Lorcan-L/cad-deliverables/hw73005-l2000/previews/A01-page-01.png

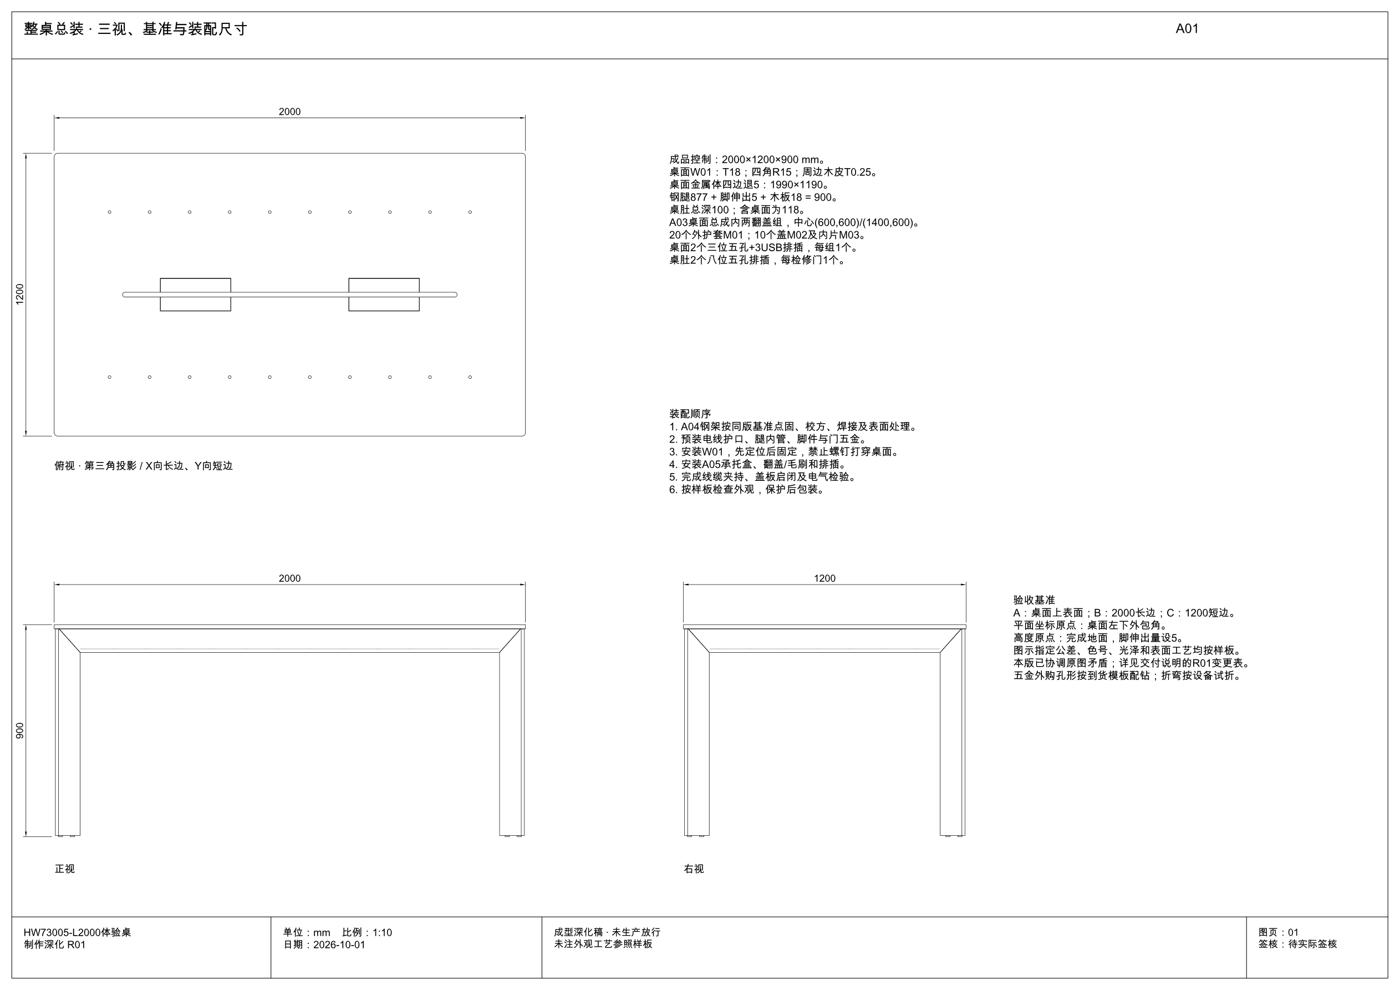
hw73005-l2000/previews/A01-page-01.png
