Lorcan-L/cad-deliverables/hw73005-l2000/previews/A02-page-02.png

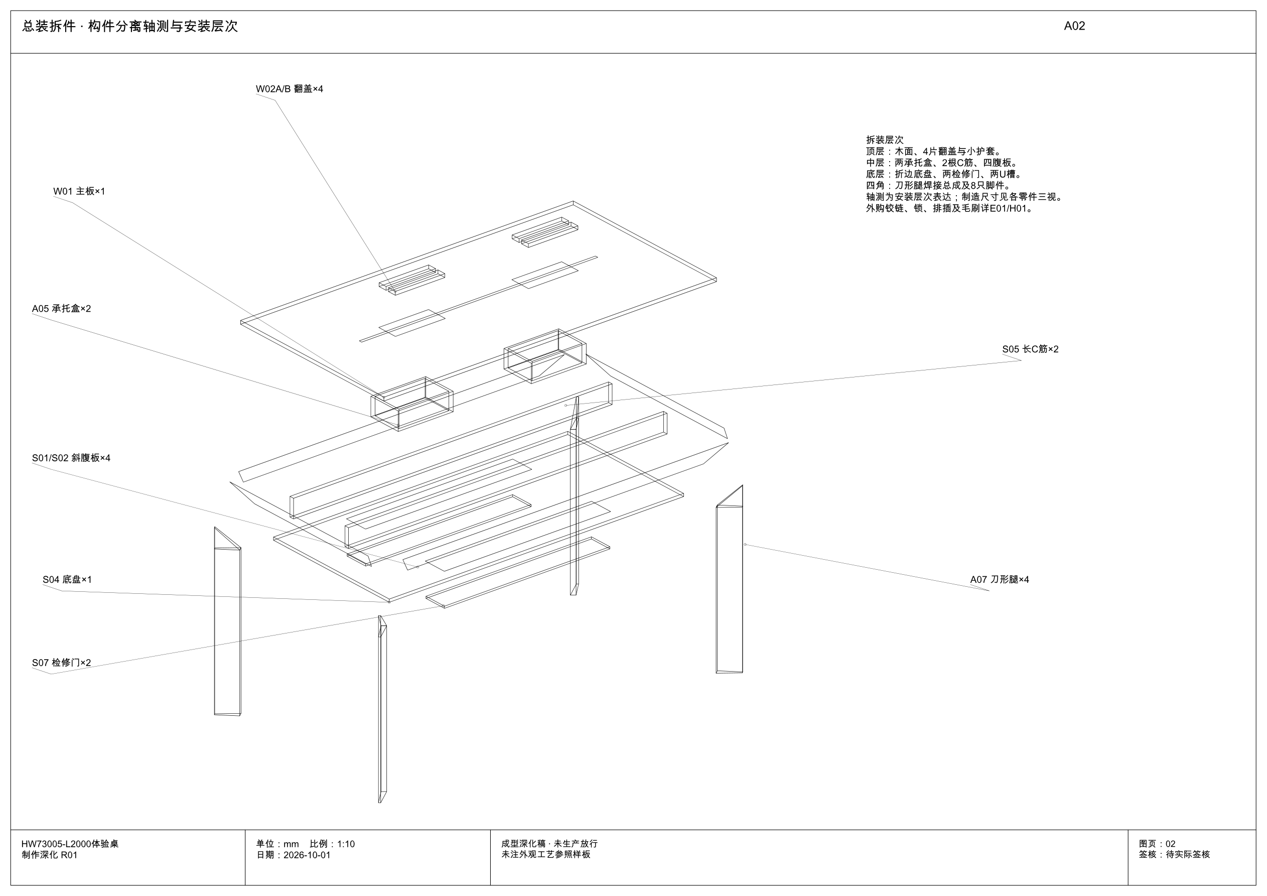
hw73005-l2000/previews/A02-page-02.png
