Lorcan-L/cad-deliverables/hw73005-l2000/previews/M01-page-21.png

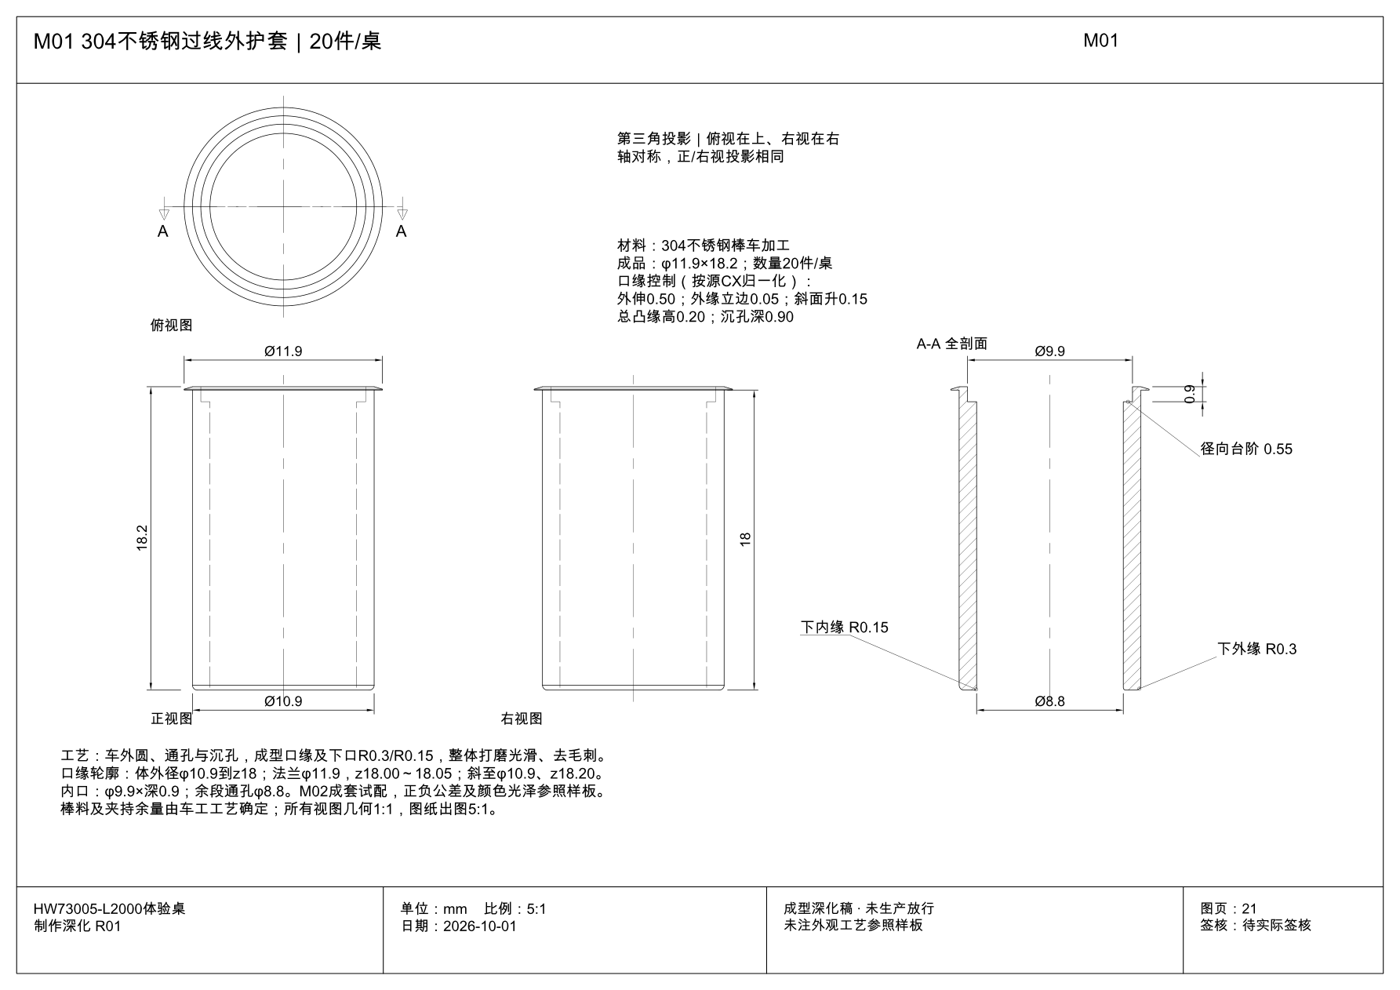
hw73005-l2000/previews/M01-page-21.png
