Lorcan-L/cad-deliverables/hw73005-l2000/previews/R02/A08-page-21.png

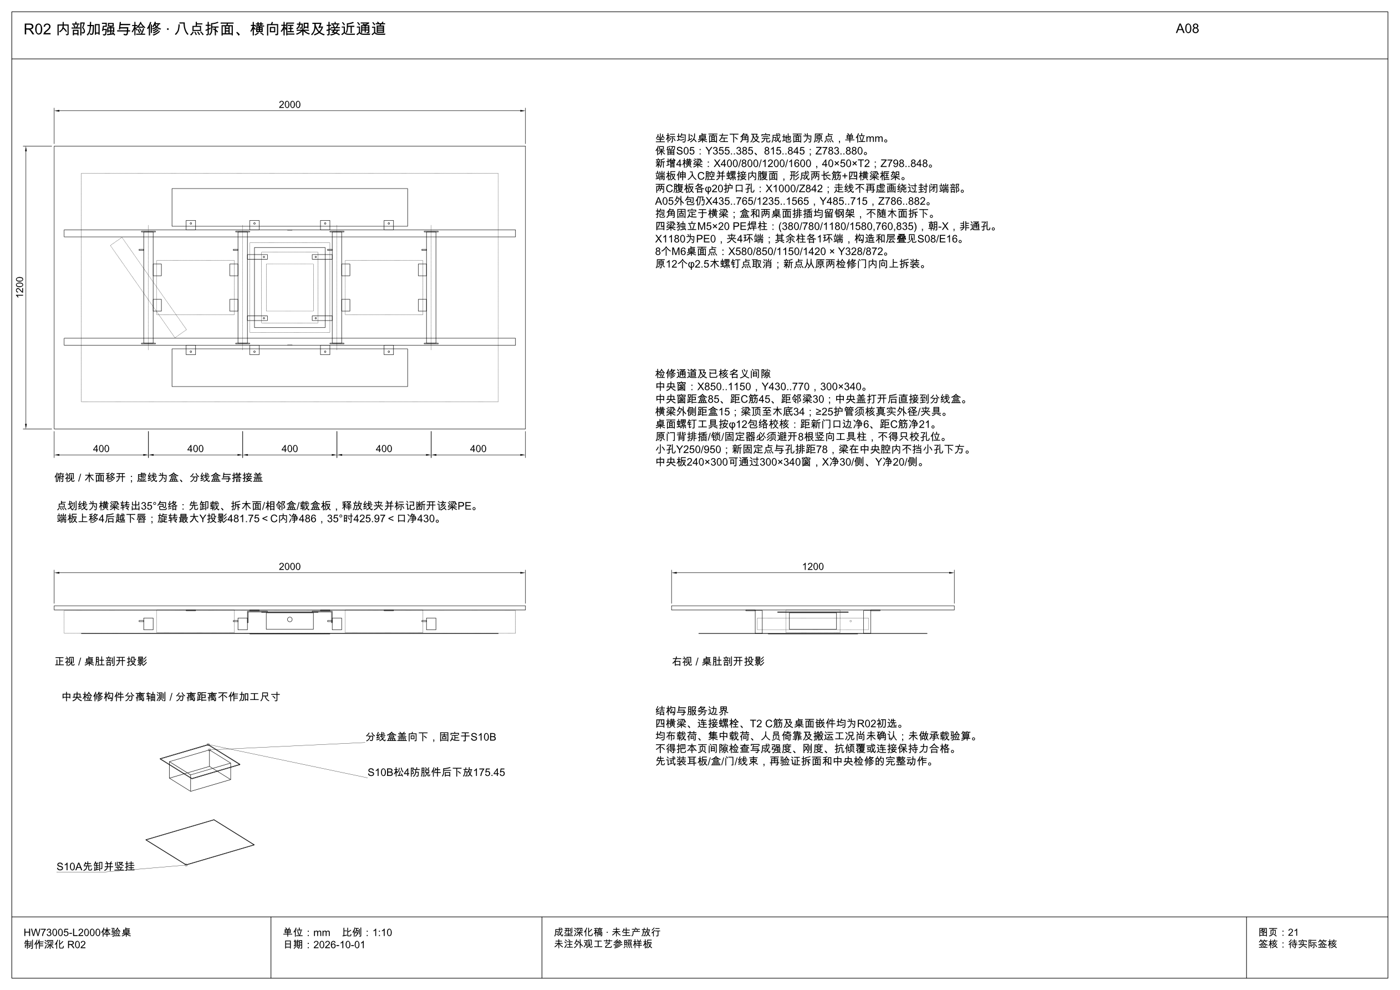
hw73005-l2000/previews/R02/A08-page-21.png
