Lorcan-L/cad-deliverables/hw73005-l2000/previews/R02/E02-page-32.png

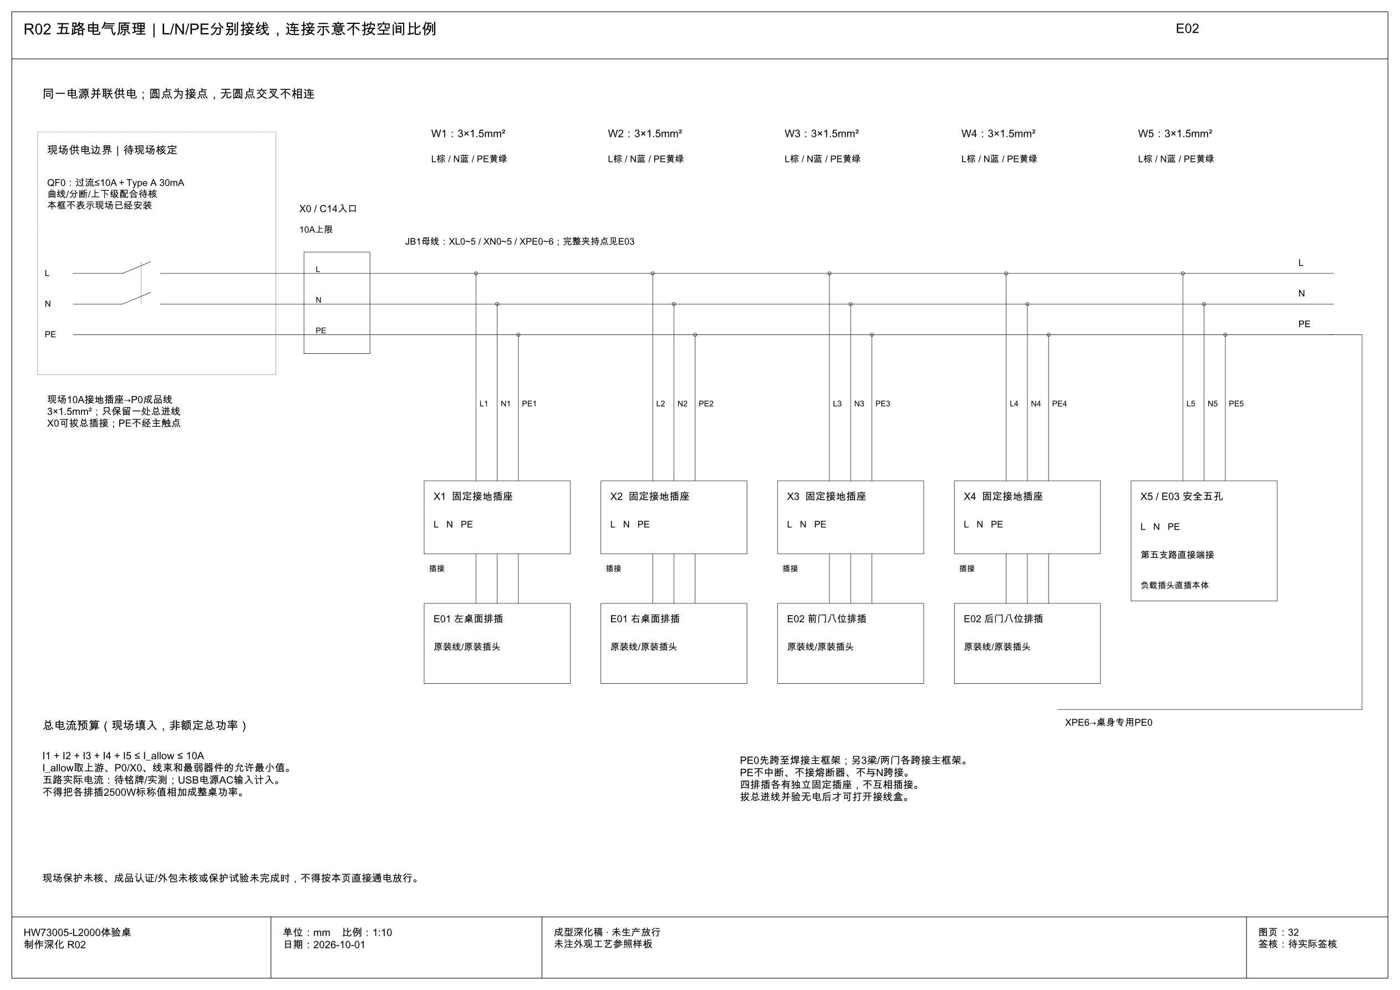
hw73005-l2000/previews/R02/E02-page-32.png
