Lorcan-L/cad-deliverables/hw73005-l2000/previews/R02/S10F-page-29.png

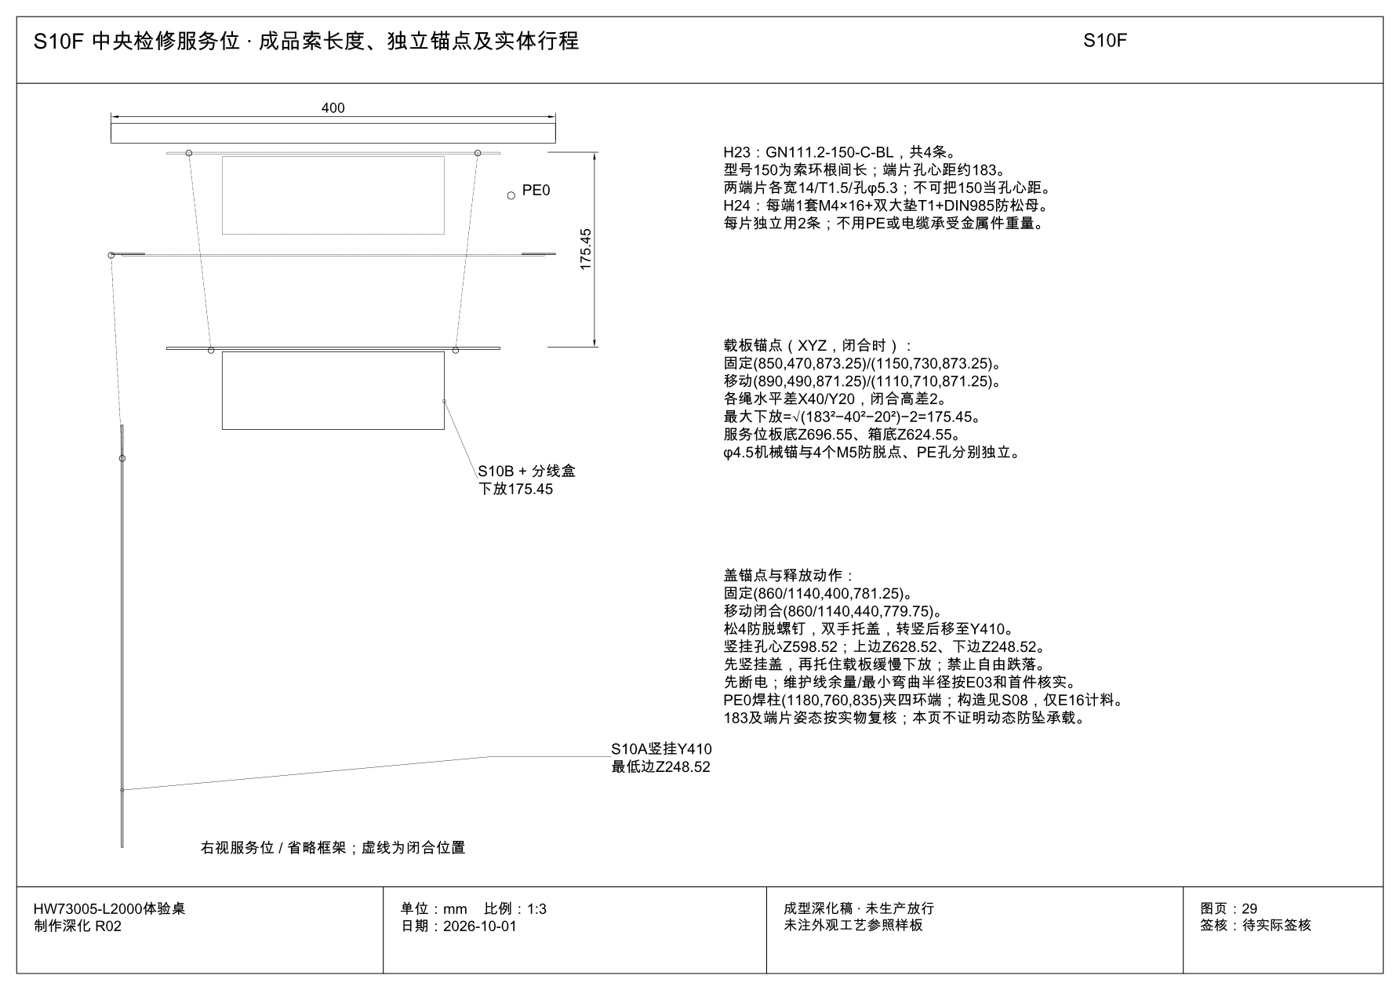
hw73005-l2000/previews/R02/S10F-page-29.png
