Lorcan-L/cad-deliverables/hw73005-l2000/previews/R03/D01-page-15.png

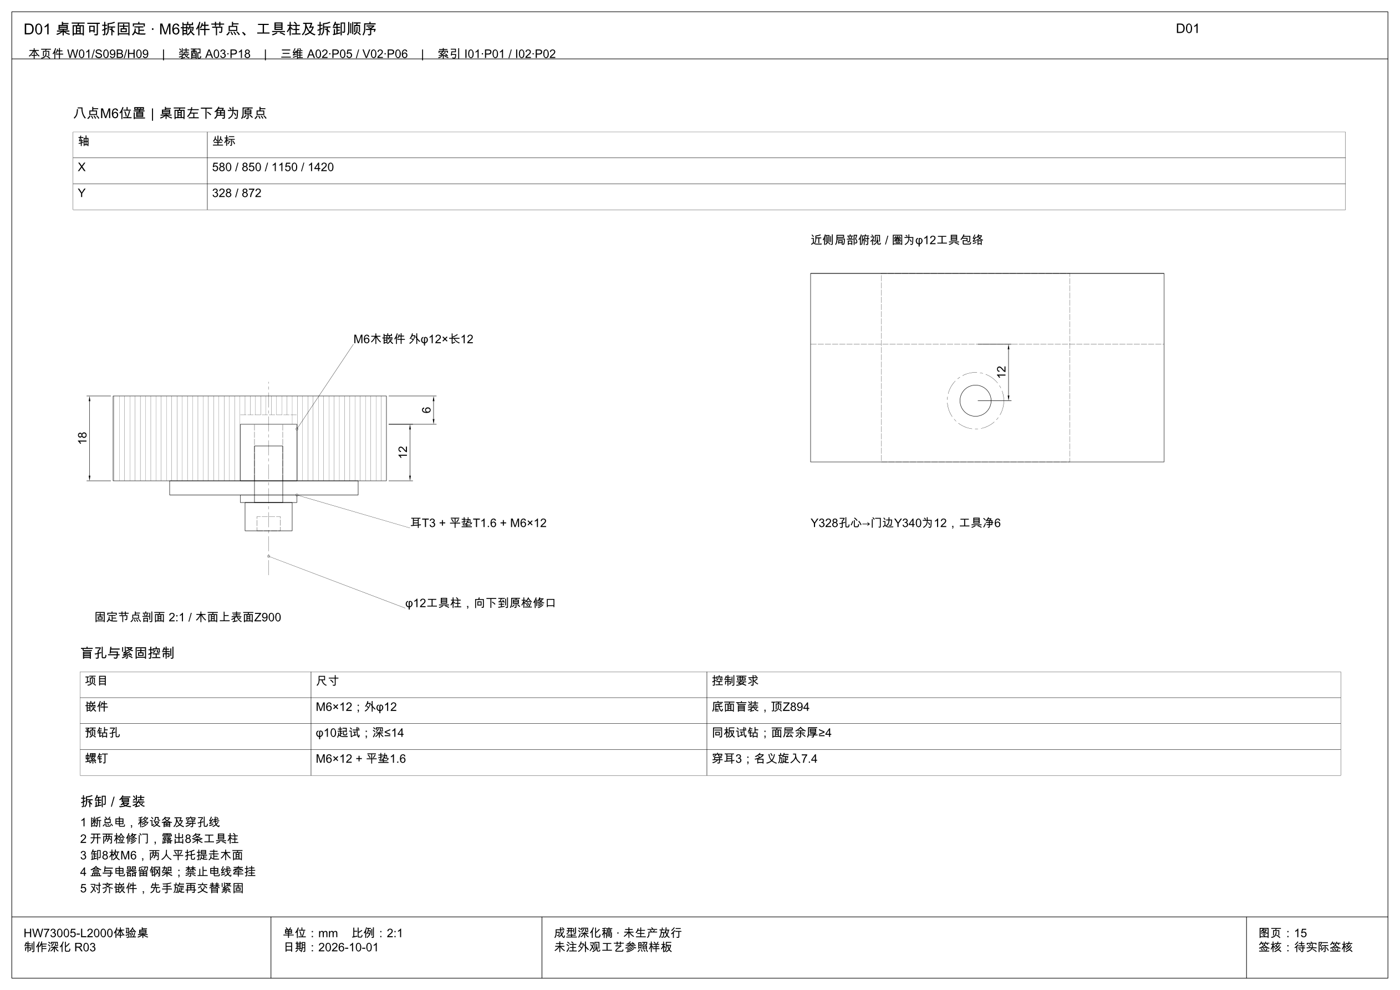
hw73005-l2000/previews/R03/D01-page-15.png
