Lorcan-L/cad-deliverables/hw73005-l2000/previews/R03/V05-page-10.png

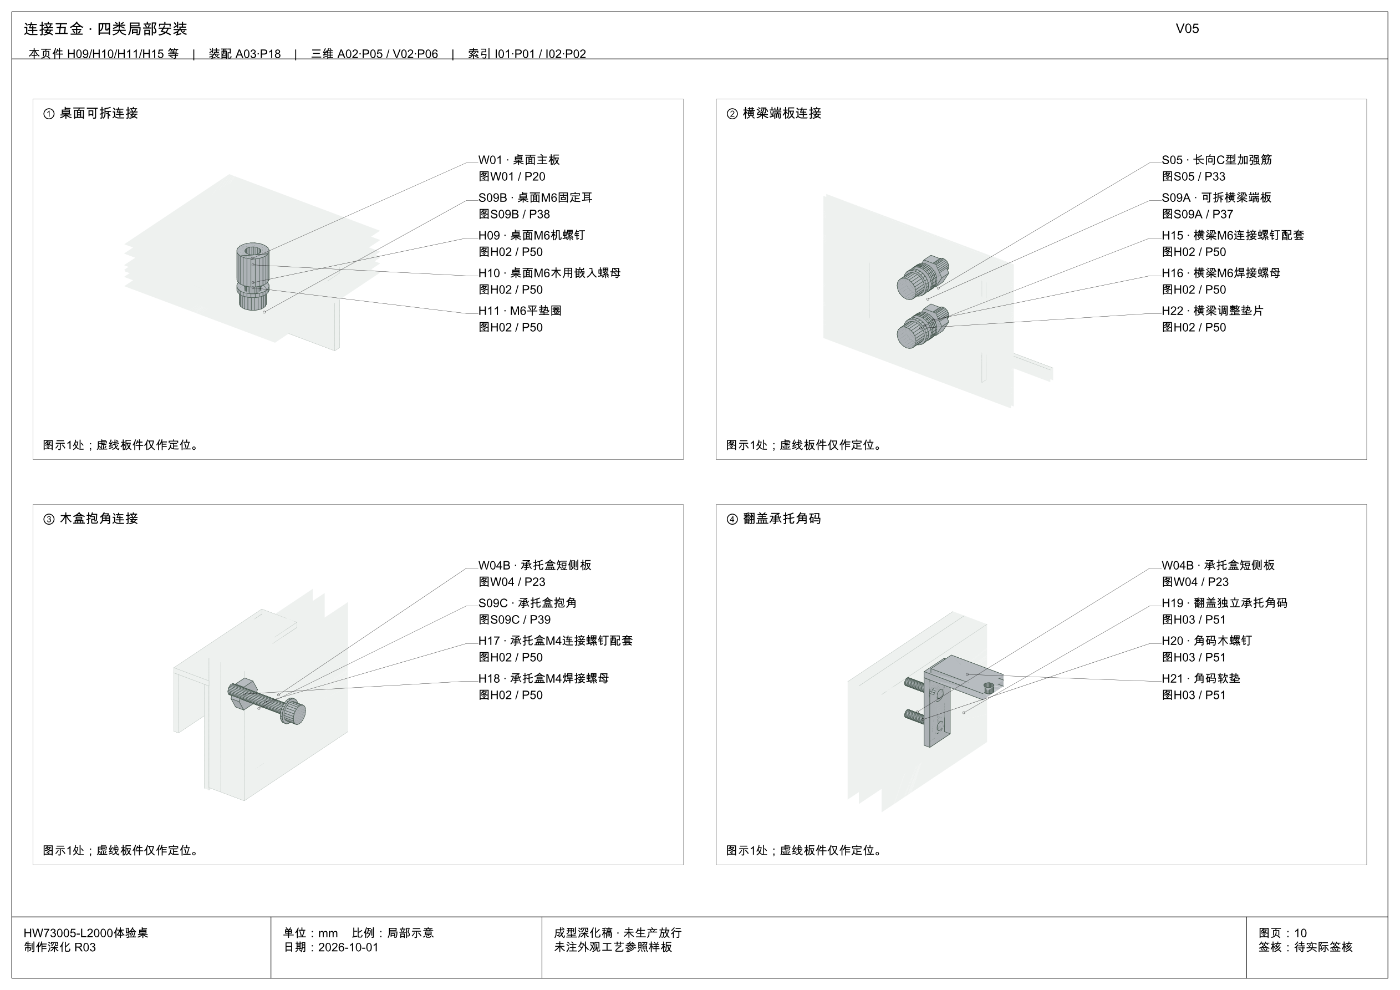
hw73005-l2000/previews/R03/V05-page-10.png
