Lorcan-L/cad-deliverables/hw73005-l2000/previews/R03/V10-page-07.png

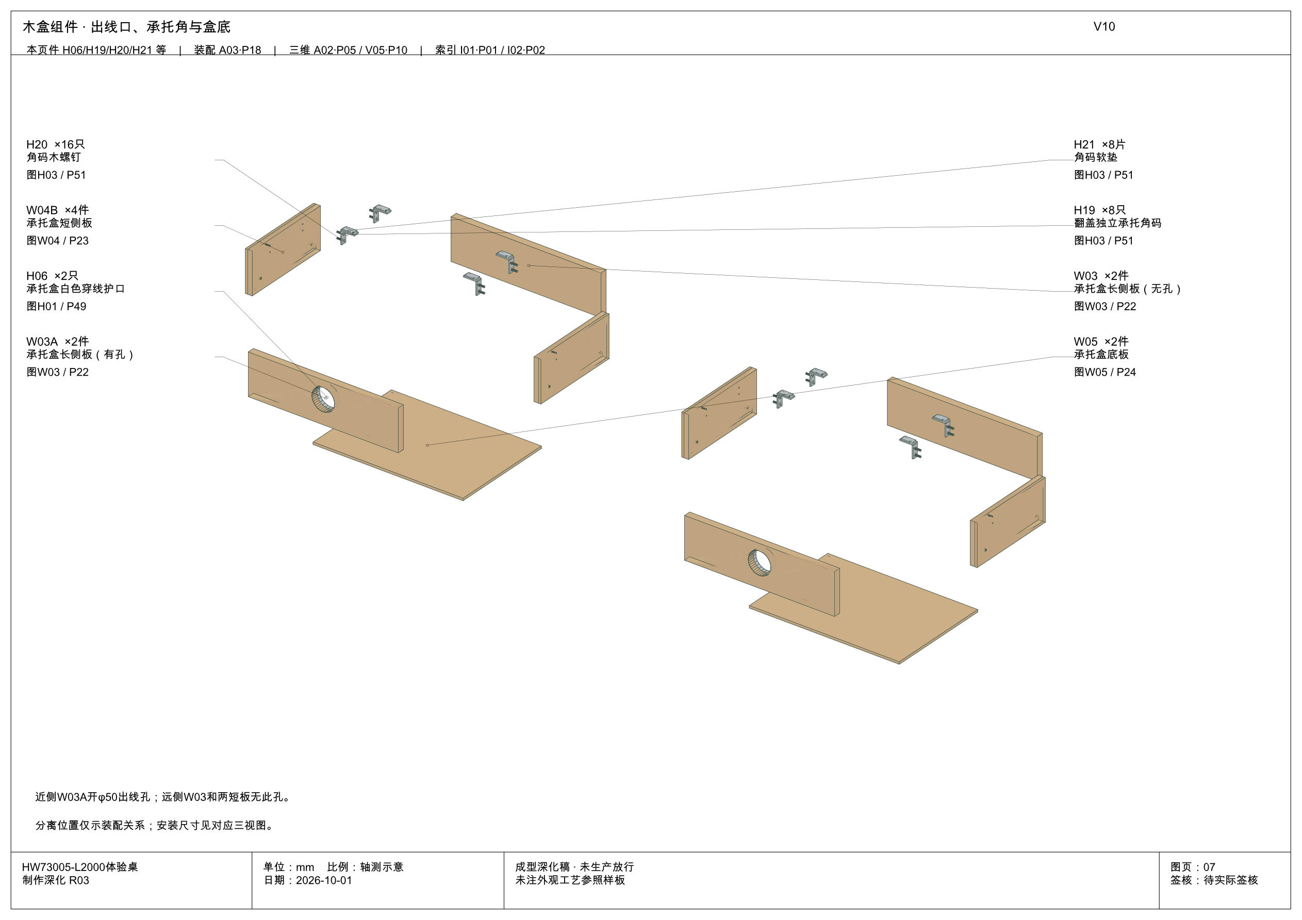
hw73005-l2000/previews/R03/V10-page-07.png
