Lorcan-L/cad-deliverables/hw73005-l2000/previews/R04/page-10.png

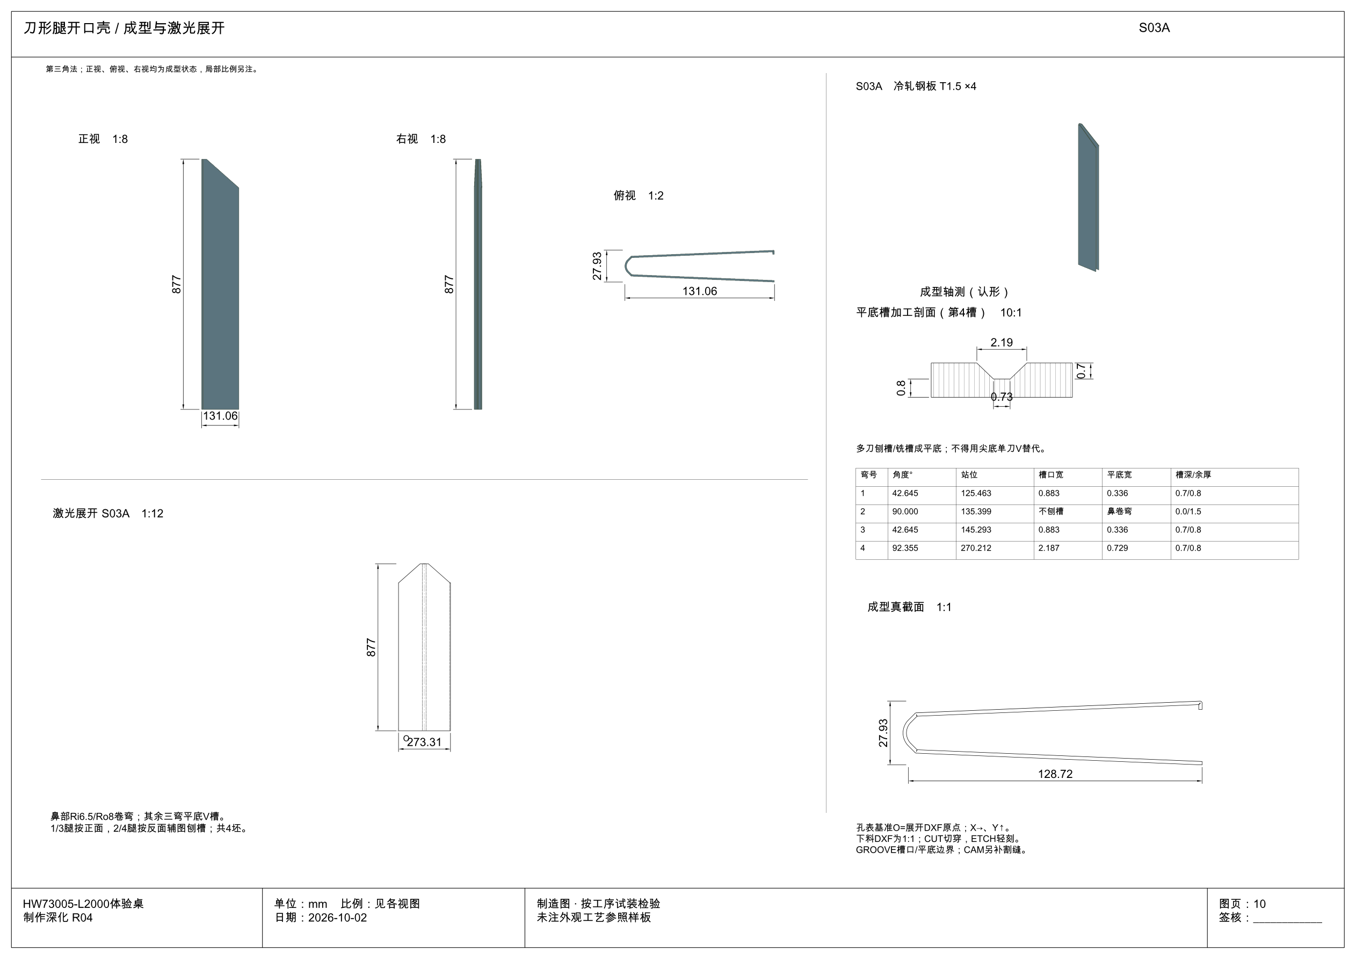
hw73005-l2000/previews/R04/page-10.png
