Lorcan-L/cad-deliverables/hw73005-l2000/previews/W01-page-06.png

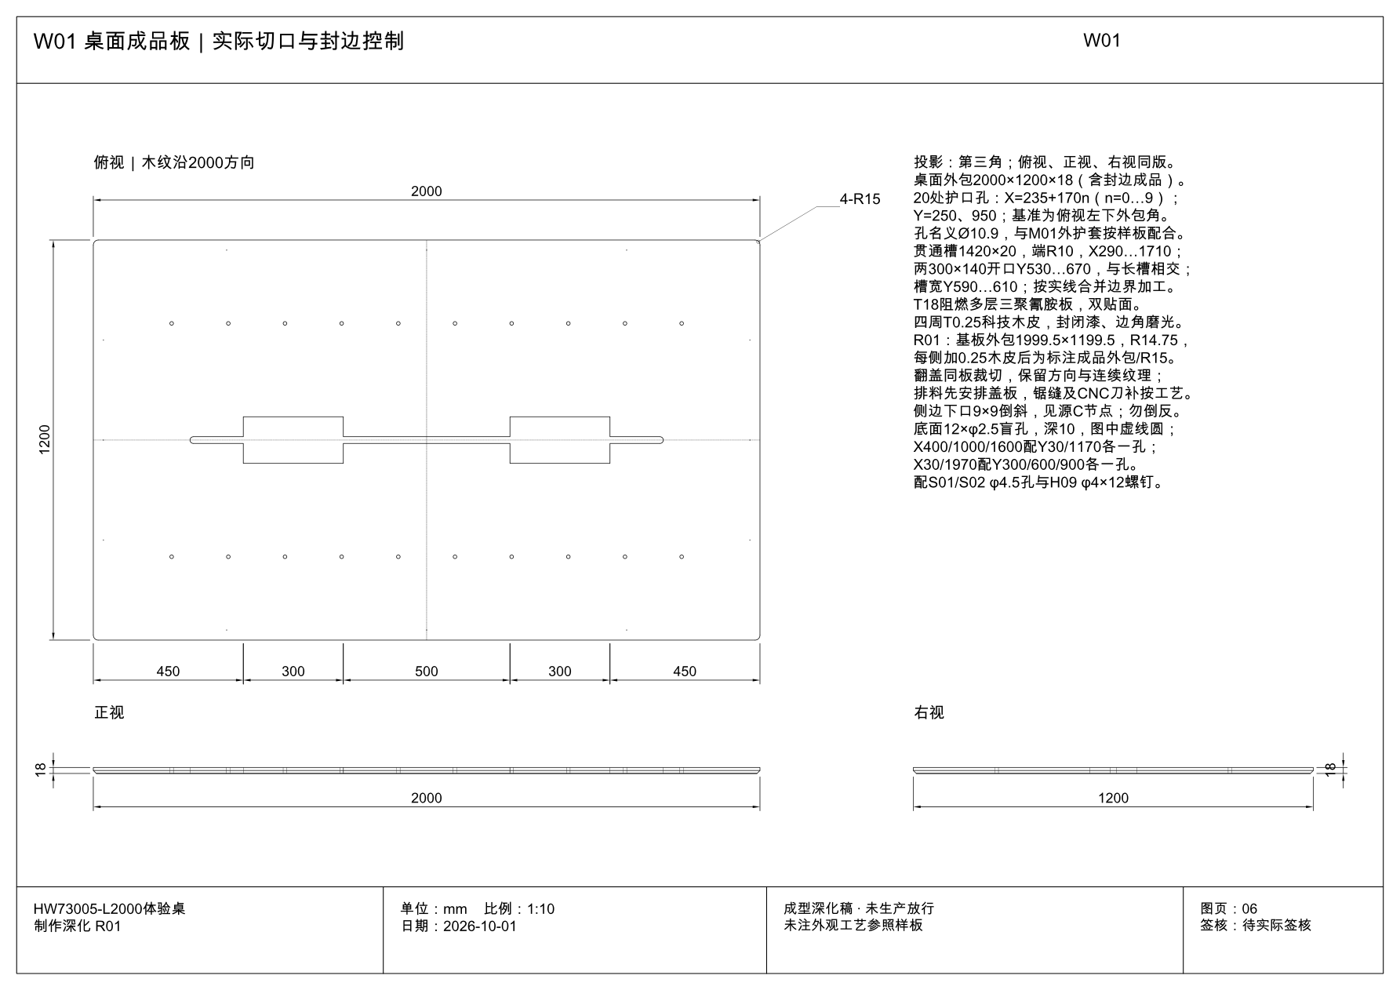
hw73005-l2000/previews/W01-page-06.png
