Lorcan-L/cad-deliverables/hw73005-l2000/files/R03/HW73005-L2000_R03_BOM.xlsx

Sheet: 零件清单
体验桌零件与采购清单
HW73005-L2000 L2000体验桌 R03 尺寸单位 mm
批量（套） | 1 |  | 版次日期 | 2026-10-01
黄色单元格为本批套数。本批数量 = 单套数量 × 套数；空白数量表示待核实。总成与子件不叠加汇总。
编号 | 零件名称 | 所属总成 | 制造 / 采购类别 | 材料 | 厚度 mm | 单套数量 | 单位 | 本批数量 | 成品尺寸 mm | 开料尺寸 mm | 工艺 / 表面处理 | 图号 | PDF 页 | 状态 | 计数口径 | 依据 | 备注
A01 | 体验桌总装 | 整桌 | 装配 | 详见子件 |  | 1 | 套 | 1 | 2000×1200×900 |  | 按图装配→试装检验 | A01 | 4 | 图纸数字核对；实物首件未执行 | 装配数量；材料按子件领用 | 顾客DWG；R02成型与检修协调 | 总成数量不重复计入领料
A04 | 焊接钢结构总成 | A01 | 装配 | 详见子件 |  | 1 | 套 | 1 | 1990×1190×882（含脚） |  | 按图装配→试装检验 | A04 | 17 | 图纸数字核对；实物首件未执行 | 装配数量；材料按子件领用 | 顾客DWG；R02成型与检修协调 | 总成数量不重复计入领料
A03 | 桌面翻盖总成 | A01 | 装配 | 阻燃多层三聚氰胺板+科技木皮 | 18 | 1 | 组 | 1 | 2000×1200×18 | 不另计材料 | 同板裁切、开槽、钻孔、封边、磨边 | A03 | 18 | 成型三视已绘；五金安装按实物配孔 | 装配数量；材料按子件领用 | 原图总装顶视及D节点；R02成品五金与可拆固定修订 | 成品含封边；R02护口孔Ø14+0.5/0；底面八点M6嵌母，按D01定位。取消原12处木螺钉孔。
A05 | 翻盖承托盒总成 | A04 | 装配 | 阻燃多层板 |  | 2 | 组 | 2 | 330×230×96；内净300×200 | 不另计材料 | 侧板围合、底板托底；M4可拆固定至钢架抱角 | A05 | 19 | 成型三视已绘；五金安装按实物配孔 | 装配数量；材料按子件领用 | 原图总装顶视及D节点；R02成品五金与可拆固定修订 | 盒留钢架；W03A长侧φ50孔朝Y485，孔心Z842。
W01 | 桌面主板 | A03 | 木作 | 阻燃多层三聚氰胺板+科技木皮 | 18 | 1 | 件 | 1 | 2000×1200×18 | 基板1999.5×1199.5×18，四周封T0.25木皮 | 同板裁切、开槽、钻孔、封边、磨边 | W01 | 20 | 成型三视已绘；五金安装按实物配孔 | 制造零件数量 | 原图总装顶视及D节点；R02成品五金与可拆固定修订 | 成品含封边；R02护口孔Ø14+0.5/0；底面八点M6嵌母，按D01定位。取消原12处木螺钉孔。
W02A | 桌面有槽翻盖板 | A03 | 木作 | 同桌面T18阻燃多层三聚氰胺板 | 18 | 2 | 件 | 2 | 298×58×18，底侧28×7让位 | 同W01原板顺纹裁切；保留锯缝工艺量 | 同板取料、开让位、磨边、五金配孔 | W02 | 21 | 成型三视已绘；五金安装按实物配孔 | 制造零件数量 | 原图总装顶视及D节点；R02成品五金与可拆固定修订 | 源D 0x8469…0x846e；R01长度298；安装在开口Y低值侧，槽口朝中央毛刷。
W02B | 桌面实截面翻盖板 | A03 | 木作 | 同桌面T18阻燃多层三聚氰胺板 | 18 | 2 | 件 | 2 | 298×58×18，实截面 | 同W01原板顺纹裁切；保留锯缝工艺量 | 同板取料、磨边、五金配孔 | W02 | 21 | 成型三视已绘；五金安装按实物配孔 | 制造零件数量 | 原图总装顶视及D节点；R02成品五金与可拆固定修订 | 源D 0x8465…0x8468；R01长度298；安装在开口Y高值侧，不复制A盖让位槽。
W03 | 承托盒长侧板（无孔） | A05 | 木作 | 阻燃多层板 | 15 | 2 | 件 | 2 | 330×91×15 | 按成品净形 | 裁切、磨边、饰面、试装配孔 | W03 | 22 | 成型三视已绘；五金安装按实物配孔 | 制造零件数量 | 原图总装顶视及D节点；R02成品五金与可拆固定修订 | 远侧Y700..715，每盒1片。
W03A | 承托盒长侧板（有孔） | A05 | 木作 | 阻燃多层板 | 15 | 2 | 件 | 2 | 330×91×15，φ50孔中心165/51 | 按成品净形 | 裁切、开φ50孔、护口试装、磨边 | W03 | 22 | 成型三视已绘；五金安装按实物配孔 | 制造零件数量 | 原图总装顶视及D节点；R02成品五金与可拆固定修订 | 近侧Y485..500；孔心全局(600/1400,492.5,842)，孔朝-Y。
W04B | 承托盒短侧板 | A05 | 木作 | 阻燃多层板 | 15 | 4 | 件 | 4 | 200×91×15 | 按成品净形 | 裁切、2×φ4.5通孔、4×φ2深10盲孔、磨边 | W04 | 23 | 成型三视已绘；五金安装按实物配孔 | 制造零件数量 | 原图总装顶视及D节点；R02成品五金与可拆固定修订 | 固定孔u25/175 v24；承托盲孔u52/148 v64.77/77.77。无过线孔。
W05 | 承托盒底板 | A05 | 木作 | R01选用阻燃多层板 | 5 | 2 | 件 | 2 | 330×230×5 | 按成品净形 | 裁切、磨边、围板托底装配 | W05 | 24 | 成型三视已绘；五金安装按实物配孔 | 制造零件数量 | 原图总装顶视及D节点；R02成品五金与可拆固定修订 | T5为源D节点实线归一结果；材质选用在R01声明。
S01 | 长边斜腹板 | A04 | 钣金 | 冷轧钢板 | 1.5 | 2 | 件 | 2 | 上口1958.5 / 下口1779.06 × 高100；截面横包110.3 | 按成型图、实际板材与折弯机试折反算 | 激光切割→折弯/成型→端口放样→点固校方→焊接打磨→按样板表面处理 | S01 | 26 | 成型控制；展开补偿按设备首件 | 制造零件数量 | 顾客DWG有效图形 + R01分片 | 颜色、光泽、焊缝处理按样板；去毛刺、不得割手
S02 | 短边斜腹板 | A04 | 钣金 | 冷轧钢板 | 1.5 | 2 | 件 | 2 | 上口1158.5 / 下口979.056 × 高100；截面横包110.3 | 按成型图、实际板材与折弯机试折反算 | 激光切割→折弯/成型→端口放样→点固校方→焊接打磨→按样板表面处理 | S02 | 27 | 成型控制；展开补偿按设备首件 | 制造零件数量 | 顾客DWG有效图形 + R01分片 | 颜色、光泽、焊缝处理按样板；去毛刺、不得割手
A07 | 刀形桌腿焊接总成 | A04 | 装配 | 冷轧钢板 + M8脚件 |  | 4 | 组 | 4 | 131.062×27.933×882（含脚5） |  | 点固→校正→焊接→打磨→装脚 | A07 | 28 | R01分片与高度修正 | 装配数量；材料按子件领用 | 顾客DWG有效图形 + R01分片 | 颜色、光泽、焊缝处理按样板；去毛刺、不得割手
S03A | 刀形腿开口壳 | A07 | 钣金 | 冷轧钢板 | 1.5 | 4 | 件 | 4 | 131.062×27.933×877（低端777） | 按成型图、实际板材与折弯机试折反算 | 激光切割→包折/卷弯→焊接打磨 | S03A | 29 | 成型控制；首件顶口放样 | 制造零件数量 | 顾客DWG有效图形 + R01分片 | 颜色、光泽、焊缝处理按样板；去毛刺、不得割手
S03B | 刀形腿内端封板 | A07 | 钣金 | 冷轧钢板 | 1.5 | 4 | 件 | 4 | 24.733×777×1.5 | 24.733×777×1.5 | 激光切割→焊接→打磨 | S03BC | 30 | 成型控制；展开补偿按设备首件 | 制造零件数量 | 顾客DWG有效图形 + R01分片 | 颜色、光泽、焊缝处理按样板；去毛刺、不得割手
S03C | 刀形腿底封板 | A07 | 钣金 | 冷轧钢板 | 1.5 | 4 | 件 | 4 | 随壳内轮廓配切；外包≤128.1×24.9 | 沿S03A成型内轮廓留0.2间隙 | 内轮廓套样→切孔→焊母→焊接 | S03BC | 30 | 配切件；按首件成型内腔 | 制造零件数量 | 顾客DWG有效图形 + R01分片 | 颜色、光泽、焊缝处理按样板；去毛刺、不得割手
S04 | 桌肚四边折边底盘 | A04 | 钣金 | 冷轧钢板 | 1 | 1 | 件 | 1 | 1769.4×969.4×15 | 按成型图、实际板材与折弯机试折反算 | 切割→四边折弯→焊接 | S04 | 31 | R02门框、X0与中央口接口；展开按实际折弯补偿 | 制造零件数量 | 顾客DWG有效图形 + R01分片 | 颜色、光泽、焊缝处理按样板；去毛刺、不得割手
S07 | 桌肚检修门 | A04 | 钣金 | 冷轧钢板 | 1.5 | 2 | 件 | 2 | 994.8×154.8×10 | 按成型图、实际板材与折弯机试折反算 | 成品接口切孔→折弯→装五金→启闭检查 | S07 | 32 | 成品型号孔图已纳入；到货同版复核 | 制造零件数量 | 顾客DWG有效图形 + R01分片 | 颜色、光泽、焊缝处理按样板；去毛刺、不得割手
S05 | 长向C型加强筋 | A04 | 钣金制造件 | 冷轧钢板 | 2 | 2 | 件 | 2 | 最大投影1943×30×97；上边1915.4；下边1767 |  | T2切孔折弯；两端阶梯/斜切；8×φ6.6及1×φ20每根；焊装 | S05 | 33 | 成型已绘；工艺试制待核 | 制造零件数量 | 源BV-BV 0x7EC7..0x7EF2；D节点0x84A2..0x84D5；R01包络与筋距统一 | 每桌2根；唇边13，C口相向；净430/外跨490。端接口、折弯补偿与焊接收缩未放行。
S06 | U型卡槽 | A04 | 钣金制造件 | 冷轧钢板 | 1 | 2 | 件 | 2 | 100长×25底宽×20高；喉口18 |  | T1折弯；口沿外翻；与底板焊接；表面处理随金属总成 | S06 | 34 | 成型已绘；工艺试制待核 | 制造零件数量 | 源U型卡槽0xD353..0xD35F及18/20/25/100标注；R01按T1归整 | 底宽不含外翻唇；中心(315.5,595)/(1674.5,595)，相距1359；先试卡，展开补偿待核。
A08 | 桌肚内部加强与检修总成 | A04 | 装配 | 钢制结构及可拆连接 |  | 1 | 组 | 1 | 沿用2000×1200×900；详子件 |  | 按成型三视制作→去毛刺→试装→按样板表面处理 | A08 | 35 | R02成型与检修包络；承载/连接强度/首件未验证 | 装配数量；材料按子件领用 | R02用户要求；保留R01外包、C筋与承托盒；新增服务结构 | 装配项不重复领料；首件与载荷待核
S08 | 可拆横梁焊接总成 | A08 | 装配 | 钢矩管+端板+焊母 |  | 4 | 组 | 4 | 478×60×60；管身40×50×472 |  | 按成型三视制作→去毛刺→试装→按样板表面处理 | S08 | 36 | R02成型与检修包络；承载/连接强度/首件未验证 | 装配数量；材料按子件领用 | R02用户要求；保留R01外包、C筋与承托盒；新增服务结构 | 4×M6/组；子件另计
S08A | 横梁矩管身 | S08 | 钣金制造件 | 钢矩形管，牌号待载荷确认 | 2 | 4 | 件 | 4 | 40×50×T2，L472 |  | 按成型三视制作→去毛刺→试装→按样板表面处理 | S08 | 36 | R02成型与检修包络；承载/连接强度/首件未验证 | 制造零件数量 | R02用户要求；保留R01外包、C筋与承托盒；新增服务结构 | 截面是初选；不能据此宣称承载通过
S09A | 可拆横梁端板 | S08 | 钣金制造件 | 钢板 | 3 | 8 | 件 | 8 | 60×60×3；2-φ8 H11@(30,18)/(30,42) |  | 按成型三视制作→去毛刺→试装→按样板表面处理 | S09A | 37 | R02成型与检修包络；承载/连接强度/首件未验证 | 制造零件数量 | R02用户要求；保留R01外包、C筋与承托盒；新增服务结构
S09B | 桌面M6固定耳 | A08 | 钣金制造件 | 钢板 | 3 | 8 | 件 | 8 | X宽40×水平40×高35；T3；6.6×12槽 |  | 按成型三视制作→去毛刺→试装→按样板表面处理 | S09B | 38 | R02成型与检修包络；承载/连接强度/首件未验证 | 制造零件数量 | R02用户要求；保留R01外包、C筋与承托盒；新增服务结构 | 顶面Z882；沿两C筋外侧焊接；旧木螺钉接口取消
S09C | 承托盒抱角 | A08 | 钣金制造件 | 钢板 | 2 | 8 | 件 | 8 | Y宽50×X包35×Z高49；T2；側φ6 H11 |  | 按成型三视制作→去毛刺→试装→按样板表面处理 | S09C | 39 | R02成型与检修包络；承载/连接强度/首件未验证 | 制造零件数量 | R02用户要求；保留R01外包、C筋与承托盒；新增服务结构 | 同件左右各4；右向绕Z转180°装；M4从盒内拆装
S10A | 中央搭接检修盖 | A08 | 钣金制造件 | 钢板 | 1.5 | 1 | 件 | 1 | 340×380×1.5；开口300×340 |  | 按成型三视制作→去毛刺→试装→按样板表面处理 | S10 | 40 | R02成型与检修包络；承载/连接强度/首件未验证 | 制造零件数量 | R02用户要求；保留R01外包、C筋与承托盒；新增服务结构 | 4防脱M5+2防坠线；卸下竖挂后露出窗口
S10B | 分线盒吊检修安装板 | A08 | 钣金制造件 | 钢板 | 2 | 1 | 件 | 1 | 240×300×2；4-M5防脱吊点 |  | 按成型三视制作→去毛刺→试装→按样板表面处理 | S10 | 40 | R02成型与检修包络；承载/连接强度/首件未验证 | 制造零件数量 | R02用户要求；保留R01外包、C筋与承托盒；新增服务结构 | 由S10C支承；盒孔依厂家模板；下放175.45；2独立吊线
S10C | 分线盒检修板悬臂 | A08 | 钣金制造件 | 钢板 | 3 | 4 | 件 | 4 | 沿Y20×X包85×Z高49；T3 |  | 按成型三视制作→去毛刺→试装→按样板表面处理 | S10C | 41 | R02成型与检修包络；承载/连接强度/首件未验证 | 制造零件数量 | R02用户要求；保留R01外包、C筋与承托盒；新增服务结构 | 同件左右转180°装；焊于邻梁；M5焊母另计
S10D | 中央盖M5焊母补强片 | A08 | 钣金制造件 | 钢板 | 2 | 4 | 件 | 4 | 20×20×2；中心φ7 H11 |  | 按成型三视制作→去毛刺→试装→按样板表面处理 | S10DE | 42 | R02成型与检修包络；承载/连接强度/首件未验证 | 制造零件数量 | R02用户要求；保留R01外包、C筋与承托盒；新增服务结构 | 焊在底盘内面；不改变1.5+1+2紧固叠层
S10E | 检修门锁接收槽形座 | A08 | 钣金制造件 | 冷轧钢板 | 1.5 | 2 | 件 | 2 | 30×12×18.3；T1.5 |  | 按成型三视制作→去毛刺→试装→按样板表面处理 | S10DE | 42 | R02成型与检修包络；承载/连接强度/首件未验证 | 制造零件数量 | R02用户要求；保留R01外包、C筋与承托盒；新增服务结构 | 接收面Z801.3；与锁舌0.2名义间隙、搭接10.4，须首件试扣
E01 | 桌面三位五孔+3USB排插 | A04 | 电气采购 | 定型采购 |  | 2 | 个 | 2 | 每盒1个；公牛UU3653候选(1A+2C) | 成品采购；按安装接口和同版证据选配 | 原装插头接X1/X2 | E06 | 48 | 数量与接口已定；产品适用认证/到货模板/实物验收待核 | 采购数量 | R03装配导航；R02电气采购证据与R03孔路线数据 | 若需3USB-A须另选；厂家未给到货外包，实插净空待验
E02 | 桌肚八位五孔排插 | S07 | 电气采购 | 定型采购 |  | 2 | 个 | 2 | 公牛GN-604候选；每门1个 | 成品采购；按安装接口和同版证据选配 | 原装插头接X3/X4 | E05 | 47 | 数量与接口已定；产品适用认证/到货模板/实物验收待核 | 采购数量 | R03装配导航；R02电气采购证据与R03孔路线数据 | 门内验收包络400×100×86.5含固定器/插头；非厂家外形，须到货实插
E03 | 明装安全五孔插座 | A01 | 电气采购 | 定型采购 |  | 1 | 个 | 1 | 10A接地安全型；NEW1-C11100A候选 | 成品采购；按安装接口和同版证据选配 | 第五支路X5直接端子接线 | E01 | 43 | 数量与接口已定；产品适用认证/到货模板/实物验收待核 | 采购数量 | R03装配导航；R02电气采购证据与R03孔路线数据 | 型号CCC、厂家接线图和外包待核，不锁定孔距
E04 | 三芯内部分支线束 | A01 | 电气辅材 | 定型采购 |  |  | m |  | 3×1.5mm²；W00/W1~W5 | 成品采购；按安装接口和同版证据选配 | 按实测配长、端头压接、套号 | E01 | 43 | 长度待实测；未填0或估算领料 | 采购数量 | R03装配导航；R02电气采购证据与R03孔路线数据 | W00外径≤8.5且厂家静态弯曲半径≤30；活动段另核；不剪改排插原线
E05 | 桌肚过线保护管 | A01 | 电气辅材 | 定型采购 |  |  | m |  | 实际外径≤25；本版过梁层净34 | 成品采购；按安装接口和同版证据选配 | 成品护管/管口保护及固定 | E05 | 47 | 长度待实测；未填0或估算领料 | 采购数量 | R03装配导航；R02电气采购证据与R03孔路线数据 | 源≥25管须核外径，DN25不等于外径25；不进入桌腿
E06 | 绝缘套管及线号配套 | A01 | 电气辅材 | 定型采购 |  | 1 | 套 | 1 | 黄腊管/热缩管、永久线号 | 成品采购；按安装接口和同版证据选配 | 按接线点实配 | E03 | 45 | 数量与接口已定；产品适用认证/到货模板/实物验收待核 | 采购数量 | R03装配导航；R02电气采购证据与R03孔路线数据 | 仅附加绝缘；不得替代护套、护口或封闭接线盒
E07 | 中央成品分线盒与内板 | S10B | 电气采购 | 定型采购 |  | 1 | 套 | 1 | 1557HA2GY箱体＋1557HPL内板各1 | 成品采购；按安装接口和同版证据选配 | 盖向下，配S10可下放支架 | E04 | 46 | 数量与接口已定；产品适用认证/到货模板/实物验收待核 | 采购数量 | R03装配导航；R02电气采购证据与R03孔路线数据 | 箱200×200×70；另购内板182×182×2.05，不当作默认随箱；改孔后不宣称原IP68
E08 | 排插独立固定分支插座 | A01 | 电气采购 | 定型采购 |  | 4 | 只 | 4 | X1~X4；10A接地型，GN-N1110候选 | 成品采购；按安装接口和同版证据选配 | 各接独立W1~W4，绝缘支架固定 | E01 | 43 | 数量与接口已定；产品适用认证/到货模板/实物验收待核 | 采购数量 | R03装配导航；R02电气采购证据与R03孔路线数据 | 不得用四位排插串接替代；外壳不任意钻孔
E09 | C14电源入口 | A01 | 电气采购 | 定型采购 |  | 1 | 只 | 1 | SCHURTER6100.3300；IEC10A/250V | 成品采购；按安装接口和同版证据选配 | X0(280,430,782)朝下，详S04/E03 | E04 | 46 | 数量与接口已定；产品适用认证/到货模板/实物验收待核 | 采购数量 | R03装配导航；R02电气采购证据与R03孔路线数据 | 后罩E18、快接E19、紧固E20分别计；中国适用认证待核
E10 | 国标10A/C13成品电源线 | A01 | 电气采购 | 定型采购 |  | 1 | 条 | 1 | 3×1.5mm²；PSB-10W/C13-10W候选 | 成品采购；按安装接口和同版证据选配 | 原装完整线，腿外侧可拆夹持 | E04 | 46 | 数量与接口已定；产品适用认证/到货模板/实物验收待核 | 采购数量 | R03装配导航；R02电气采购证据与R03孔路线数据 | 选定线径版本CCC与长度待核；不得剪改模压接头
E11 | L灰色直通端子 | A01 | 电气采购 | 定型采购 |  | 6 | 只 | 6 | WAGO2002-1201；XL0~XL5 | 成品采购；按安装接口和同版证据选配 | DIN35×7.5导轨装配 | E03 | 45 | 数量与接口已定；产品适用认证/到货模板/实物验收待核 | 采购数量 | R03装配导航；R02电气采购证据与R03孔路线数据 | 一夹一线；按厂家剥线10~12及压接工艺
E12 | N蓝色直通端子 | A01 | 电气采购 | 定型采购 |  | 6 | 只 | 6 | WAGO2002-1204；XN0~XN5 | 成品采购；按安装接口和同版证据选配 | 与L分隔、独立六连桥 | E03 | 45 | 数量与接口已定；产品适用认证/到货模板/实物验收待核 | 采购数量 | R03装配导航；R02电气采购证据与R03孔路线数据 | 严禁N-PE跨接；不得把单电位端子当多极
E13 | 黄绿PE端子 | A01 | 电气采购 | 定型采购 |  | 7 | 只 | 7 | WAGO2002-1207；XPE0~XPE6 | 成品采购；按安装接口和同版证据选配 | 专用接地脚及连续接地导轨 | E03 | 45 | 数量与接口已定；产品适用认证/到货模板/实物验收待核 | 采购数量 | R03装配导航；R02电气采购证据与R03孔路线数据 | XPE6接PE0，桌身/两门/中央组件独立跨接
E14 | 六位连续跨接桥 | A01 | 电气采购 | 定型采购 |  | 2 | 根 | 2 | WAGO2002-406；L/N各1根 | 成品采购；按安装接口和同版证据选配 | 分别桥接同色六端子 | E03 | 45 | 数量与接口已定；产品适用认证/到货模板/实物验收待核 | 采购数量 | R03装配导航；R02电气采购证据与R03孔路线数据 | 不得错购/020-000三对独立桥
E15 | 导轨端挡与绝缘端板 | A01 | 电气辅材 | 定型采购 |  | 1 | 套 | 1 | 210-112轨；249-116×2/2002-1291×3 | 成品采购；按安装接口和同版证据选配 | 轨35×7.5/T1；购2m截150固定于内板 | E03 | 45 | 数量与接口已定；产品适用认证/到货模板/实物验收待核 | 采购数量 | R03装配导航；R02电气采购证据与R03孔路线数据 | L/N/PE分区清晰；导轨保护接地和端子保持力待验
E16 | 金属件保护连接配套 | A01 | 电气辅材 | 定型采购 |  | 1 | 套 | 1 | 7条2.5黄绿线；FV2-5×11/FV2-4×2 | 成品采购；按安装接口和同版证据选配 | 主框架/另3梁/两门逐条跨接 | E03 | 45 | 数量与接口已定；产品适用认证/到货模板/实物验收待核 | 采购数量 | R03装配导航；R02电气采购证据与R03孔路线数据 | 含M5×20焊柱/齿平垫/锁母各10及门M4套2；套管1；中央E21~24不重计
E17 | 进线与线束固定护口配套 | A01 | 电气辅材 | 定型采购 |  | 1 | 套 | 1 | 适配线径的成品线夹/防拉脱件 | 成品采购；按安装接口和同版证据选配 | 腿外侧夹持、2只φ20/T2护口及盒出线 | E04 | 46 | 数量与接口已定；产品适用认证/到货模板/实物验收待核 | 采购数量 | R03装配导航；R02电气采购证据与R03孔路线数据 | X0独立夹护套；后罩/快接不抗拉；不破坏原装护套
E18 | C14原厂绝缘后罩 | A01 | 电气采购 | 定型采购 |  | 1 | 只 | 1 | SCHURTER RC320-03；3-125-663 | 成品采购；按安装接口和同版证据选配 | 罩住X0后端；31.2×23.5×51 | E04 | 46 | 数量与接口已定；产品适用认证/到货模板/实物验收待核 | 采购数量 | R03装配导航；R02电气采购证据与R03孔路线数据 | 原厂适配6100-3；出线口内径8.5；装配后包络至Z834
E19 | 全绝缘快接母端 | A01 | 电气采购 | 定型采购 |  | 3 | 只 | 3 | TE Connectivity735278；6.35×0.81 | 成品采购；按安装接口和同版证据选配 | X0的L/N/PE各1只；配套模具冷压 | E04 | 46 | 数量与接口已定；产品适用认证/到货模板/实物验收待核 | 采购数量 | R03装配导航；R02电气采购证据与R03孔路线数据 | 适1~1.5mm²、导体绝缘径≤3.3；按厂家拉脱/压接验收
E20 | C14入口固定紧固件 | A01 | 电气采购 | 定型采购 |  | 2 | 套 | 2 | M3×8沉头螺钉+平垫+防松螺母 | 成品采购；按安装接口和同版证据选配 | S04两φ3.5孔；孔距40 | E04 | 46 | 数量与接口已定；产品适用认证/到货模板/实物验收待核 | 采购数量 | R03装配导航；R02电气采购证据与R03孔路线数据 | 不作PE连接；实际板/法兰叠厚与突出量首件核定
E21 | 中央组件柔性PE线 | A01 | 电气采购 | 定型采购 |  | 2 | 根 | 2 | 黄绿铜软线2.5mm²；长度待实测 | 成品采购；按安装接口和同版证据选配 | S10A盖/S10B载板各1根至固定PE0 | E03 | 45 | 数量与接口已定；产品适用认证/到货模板/实物验收待核 | 采购数量 | R03装配导航；R02电气采购证据与R03孔路线数据 | 各留≥250维护余量；载板下放175.45，盖索孔心距183，按S10F全程核定；不承担吊重
E22 | 中央PE移动端M4环端子 | A01 | 电气采购 | 定型采购 |  | 2 | 只 | 2 | JST FV2-4；适1.04~2.63mm² | 成品采购；按安装接口和同版证据选配 | E21移动端各压1只；配S10的φ4.5孔 | E03 | 45 | 数量与接口已定；产品适用认证/到货模板/实物验收待核 | 采购数量 | R03装配导航；R02电气采购证据与R03孔路线数据 | 原厂工具压接；去漆接触面、防松并测连续性
E23 | 中央PE固定端M5环端子 | A01 | 电气采购 | 定型采购 |  | 2 | 只 | 2 | JST FV2-5；适1.04~2.63mm² | 成品采购；按安装接口和同版证据选配 | E21固定端各压1只；接PE0 | E03 | 45 | 数量与接口已定；产品适用认证/到货模板/实物验收待核 | 采购数量 | R03装配导航；R02电气采购证据与R03孔路线数据 | 各端独立夹紧；不得任意堆叠到短螺柱
E24 | 中央组件PE专用紧固件 | A01 | 电气采购 | 定型采购 |  | 2 | 套 | 2 | M4×10螺钉+平/齿形垫+防松螺母 | 成品采购；按安装接口和同版证据选配 | 盖孔(1000,450)、载板孔(1000,460) | E03 | 45 | 数量与接口已定；产品适用认证/到货模板/实物验收待核 | 采购数量 | R03装配导航；R02电气采购证据与R03孔路线数据 | 各1套，螺纹朝上；不得兼用防坠或结构螺钉
H01 | 薄型调节脚 | A07 | 采购五金 | 钢螺杆＋树脂底座 |  | 8 | 只 | 8 | 底φ20；M8×1.25；螺杆长15；底高6；总高21 |  | 外购成品；按型号采购并做首件配装 | H02 | 50 | 中国官方页有订购入口；库存未核 | 采购数量 | https://global.sugatsune.com/cn/zh-cn/tech/products/22772_t | TG-20；S03C内沉1，脚底名义外露5；每腿2只；调节后复核整桌900高及螺纹搭接；S03C脚孔局部u80/110、v13.9665，孔距30；不用原定制外φ18脚。厂家单件承载数据不能直接当整桌承载验收值。
H02 | M8六角焊接螺母 | S03C | 采购五金 | 可焊钢本色 |  | 8 | 只 | 8 | M8×1.25；对边14；螺母厚6.5；定位凸台径10.45最大 |  | 外购成品；按型号采购并做首件配装 | H02 | 50 | 准确规格商品/可选规格页可网购；中国配送及实时库存未核 | 采购数量 | https://www.nufast.co.uk/uploads/DIN_929.pdf | DIN 929 M8 钢本色；S03C定位孔φ10.5 H11；不能沿用原φ8.5；焊后通规检查；不采用不锈钢/A2版本与碳钢底板直接混配。到货核对定位凸台和安装孔。
H03 | 检修门可脱卸合页 | S07 | 采购五金 | SUS304 |  | 4 | 只 | 4 | 展开50×75×T1.5；4×φ3.8；孔距38×63.5；轴径6；厚向包络9.5 |  | 外购成品；按型号采购并做首件配装 | H03 | 51 | 中国官方页有订购入口；库存未核 | 采购数量 | https://global.sugatsune.com/cn/zh-cn/tech/products/21654_t?category=100218 | HG-OTA75 / 170-090-942；每门2只；孔中心相对铰链展开中心为(±19, ±31.75)；轴线方向沿75边；M3穿透连接；两只标称6kg仅为厂家条件值。轴可缩入拆门；闭合不靠铰链阻尼，另设限位。
H04 | 直槽工具转舌锁（完整套件） | S07 | 采购五金 | 锌合金锁体＋镀锌钢锁舌/螺母 |  | 2 | 套 | 2 | 面头φ28×4；开孔φ22.5与20.1方形交集；GH18；H19.5；锁舌35×20×T3（35为轴心至端） |  | 外购成品；按型号采购并做首件配装 | H03 | 51 | 国内厂家官方商城入口；须按完整套件型号订购并核库存 | 采购数量 | https://www.hengzhu.com/cn/product/587/Locks/MS705 | MS705-1-1；适门T1~5，含35长舌、螺母、止退件；锁头法兰贴门底Z782，末端接触面H19.5为Z801.5；S10E接收顶Z801.3留0.2，不能按近轴GH18定位接收面。锁舌扫掠留净。；官网旧规格表写MS705-1-1.1，当前尺寸图写MS705-1-1；订货应随附本图，以35锁舌/直槽芯版本核对，不混54长舌版本。
H05 | 排插滑拆固定器组 | S07 | 采购五金 | ABS＋3M胶 |  | 2 | 组 | 2 | 每门2套滑拆固定器；包装尺寸99.5×45×9.2非工程外形 |  | 外购成品；按型号采购并做首件配装 | H01 | 49 | 厂家直链天猫成品；活动门应用为待验证候选 | 采购数量 | https://www.lulian.cn/product/751-cn.html | LP332 / 每组2套；GN-604背部与喷涂门内面平整清洁，按厂家胶粘并充分固化；每组2套同向滑轨；不钻排插壳。活动门倒置、抗滑脱和热老化未获厂家证明，须连同用户插头做启闭/抗拉首件验证。；不把包装尺寸充当外形；承载额定、装配外包、店铺实时库存未核。
H06 | 承托盒白色穿线护口 | W03A | 采购五金 | 白色塑料 |  | 2 | 只 | 2 | φ50安装孔；两件式；经销规格入孔深22 |  | 外购成品；按型号采购并做首件配装 | H01 | 49 | 可网购具体型号；到货φ50孔配装及入孔深待复核 | 采购数量 | https://www.hafele.com/INTERSHOP/static/WFS/Haefele-HAC-Site/-/Haefele-HAC/en_US/opentext/assets/hac/Closet_Catalog_2022.pdf | 429.99.735；W03A长侧T15板φ50孔；局部u165/v51，全局(600/1400,492.5,842)，孔朝近侧-Y。筒向盒内突出约7；保持周围净空，按厂家允许压装或胶粘。可取盖穿原装插头，再恢复护口；开口及插头穿越须首件核实。；S51/WHT孔径44.2与本项目不符，已排除；不改原φ50孔为错规格。
H07 | 小翻盖隐藏桶式铰链 | A03 | 采购五金 | 黄铜 |  | 8 | 只 | 8 | 桶径10；盲孔φ10深11.5；孔心距朝开口边6.8；D≥2；E≤1.8；最小板厚12.7；开启180° |  | 外购成品；按型号采购并做首件配装 | H03 | 51 | 厂家官网可加入购物车；中国现货和进口交期未核 | 采购数量 | https://www.soss.com/product/barrel-hinge/ | BH104；T18盖及桌面均从顶面钻φ10深11.5；剩板厚6.5。每盖u50/248、孔心距外侧开合边6.8；180°展开对应桌面闭合共面，操作抬90°。；厂家仅轻型应用，无扭矩保持；闭合须8只独立角码支承。顶面可见桶式铰链金属链节；低Y毛刷安装28×7槽保留，不能误删。
H09 | 桌面M6机螺钉 | A03 | 采购五金 | 12.9级钢镀锌 |  | 8 | 只 | 8 | M6×1；公称杆长12；配平垫6.4×12×1.6 |  | 外购成品；按型号采购并做首件配装 | H02 | 50 | 准确规格商品/可选规格页可网购；中国配送及实时库存未核 | 采购数量 | https://www.nbk1560.com/en-US/products/specialscrew/nedzicom/socketheadcapscrew/SNS/ | ISO 4762 / DIN 912 M6×12；穿T3固定耳＋T1.6垫片，进入桌面嵌母7.4；由桌下拆装；成对点X580/850/1150/1420×Y328/872；8点为R02设计数量；拧紧扭矩按实际阻燃多层板试验，不能套用钢连接满扭矩。
H10 | 桌面M6木用嵌入螺母 | W01 | 采购五金 | 镀锌钢 |  | 8 | 只 | 8 | 外径12；L12；内牙M6；内六角SW6；厂家底孔10.0~10.5 |  | 外购成品；按型号采购并做首件配装 | H02 | 50 | 厂家官网可在线订购；中国现货和进口交期未核 | 采购数量 | https://www.rampa.com/eu/en/rampa-inserts-type-skd30/439612001010 | SKD30 439612001；从桌面底安装；试样底孔φ10.5深14、面层最小保留4；嵌件法兰与底面齐，深度限位钻孔；底孔深14是本项目T18安全余量设计，厂家仅提供底孔直径范围；在同批阻燃板试装/拔出检查后放行。不拿京东泛称M6×12未知外径件直接代换。
H11 | M6平垫圈 | A03 | 采购五金 | 镀锌钢 |  | 8 | 只 | 8 | φ6.4×φ12×T1.6 |  | 外购成品；按型号采购并做首件配装 | H02 | 50 | 准确规格商品/可选规格页可网购；中国配送及实时库存未核 | 采购数量 | https://www.mofakult.fr/en/washer-m6-6-4-12-1-6-galvanized-29733 | ISO 7089 / DIN 125-A 6；与8只M6×12配套；覆盖6.6×12长圆调节孔；不要用不同厚度弹垫替代，否则有效啮合长度变化。
H12 | 检修门合页螺钉配套 | S07 | 采购五金 | 不锈钢 |  | 16 | 套 | 16 | M3×0.5×8；每合页4套 |  | 外购成品；按型号采购并做首件配装 | H03 | 51 | 准确规格商品/可选规格页可网购；中国配送及实时库存未核 | 采购数量 | https://www.vital-parts.co.uk/phillips-pan-head-machine-screws-din-7985h/17017-pph7985h-m3-8-a2 | M3×8盘头＋M3防松螺母＋M3平垫；穿φ3.8合页孔与门/底盘配孔；每套1螺钉1平垫1防松螺母；组装后验轴芯可操作；合页叶片T1.5＋门T1.5（或支撑板）；M3×8避免长端侵入活动区。
H13 | 检修盖及吊板防脱螺钉 | A04 | 采购五金 | SUSXM7（SUS304同等） |  | 8 | 只 | 8 | M5×0.8；杆长8；末端牙长4；颈径3.9；头φ8.5×5；内六角4 |  | 外购成品；按型号采购并做首件配装 | H02 | 50 | NBK中国官方询价/官方1688渠道；库存未核 | 采购数量 | https://www.nbk1560.com/en-US/products/specialscrew/nedzicom/captivescrew/SSC/SSC-M5/SSC-M5-8/ | SSC-M5-8；中央盖4：T1.5攻M5防脱＋T1底盘＋T2补强＋DIN929 M5，夹紧栈4.5，啮合3.5。吊板4：T2攻M5防脱＋T3臂＋DIN929 M5，夹紧栈5，啮合3。；盖4点(840/1160,450/750)；吊板4点(890/1110,470/730)。SSC末牙4、颈4；不换长10型号。
H25 | 成品过线衬套 | A06 | 采购五金 | 锌合金ZDC黑色 |  | 20 | 只 | 20 | 外缘φ18；嵌入φ14；内孔φ12；总高18；法兰高2 |  | 外购成品；按型号采购并做首件配装 | A06 | 52 | 厂家美国官网可按只加购物车；中国配送和库存未核 | 采购数量 | https://www.sugatsune.com/content/site-assets/201B_PDF/CHC-S.pdf | CHC-S18BL；W01孔φ14+0.5/0；按桌面/设备过线设计装20只；衬套面高出桌面2；替代R01 M01/M02定制金属护套。数量与桌面接口由主装配核对，不凭图示符号加计。
H26 | 闲置孔成品盖 | A06 | 采购五金 | 塑料 |  | 10 | 只 | 10 | 适φ12孔；头φ18；H2；插杆8.4 |  | 外购成品；按型号采购并做首件配装 | A06 | 52 | 国外经销商网购500只/包；单桌用10只，中国配送及实时库存未核 | 采购数量 | https://hafelethailand.com/wp-content/uploads/2025/12/13-Tooling-Screws-and-Consumables.pdf | 045.00.332；装入CHC-S18BL内φ12；组合总突出约4；首件实配通过前不得当认证配套；与LAMP衬套属于跨品牌组合，需确认卡紧、拔出力及顶高；不伪称厂家认证套装。
H14 | 检修盖及吊板M5焊接螺母 | A04 | 采购五金 | 可焊钢本色 |  | 8 | 只 | 8 | M5×0.8；对边10；厚4；定位凸台6.96最大 |  | 外购成品；按型号采购并做首件配装 | H02 | 50 | 准确规格商品/可选规格页可网购；中国配送及实时库存未核 | 采购数量 | https://www.nufast.co.uk/uploads/DIN_929.pdf | DIN929 M5 钢本色；盖T2补强片或吊板T3臂均φ7 H11定位后焊；盖4、板4；对应SSC-M5-8。；订单具体SKU、包装量和库存待采购核对。
H15 | 横梁M6连接螺钉配套 | S09A | 采购五金 | 12.9级螺钉＋镀锌钢平垫 |  | 16 | 套 | 16 | M6×20；头下垫6.4×12×T1.6；每套各1 |  | 外购成品；按型号采购并做首件配装 | H02 | 50 | 准确规格商品/可选规格页可网购；中国配送及实时库存未核 | 采购数量 | https://www.misumi.com.cn/ | ISO4762 M6×20＋ISO7089平垫6；C筋T2＋每螺栓4mm调整片＋S09A T3端板＋DIN929M6；每端2点，共16套。；订单具体SKU、包装量和库存待采购核对。
H16 | 横梁M6焊接螺母 | S09A | 采购五金 | 可焊钢本色 |  | 16 | 只 | 16 | M6×1；对边11；厚5；定位凸台7.96最大 |  | 外购成品；按型号采购并做首件配装 | H02 | 50 | 准确规格商品/可选规格页可网购；中国配送及实时库存未核 | 采购数量 | https://www.nufast.co.uk/uploads/DIN_929.pdf | DIN929 M6 钢本色；S09A T3端板φ8 H11；焊母朝管腔；孔心(30,18)/(30,42)；订单具体SKU、包装量和库存待采购核对。
H17 | 承托盒M4连接螺钉配套 | S09C | 采购五金 | 12.9级螺钉＋镀锌钢平垫 |  | 8 | 套 | 8 | M4×25；每套1螺钉1平垫 |  | 外购成品；按型号采购并做首件配装 | H02 | 50 | 准确规格商品/可选规格页可网购；中国配送及实时库存未核 | 采购数量 | https://www.misumi.com.cn/ | M4×25＋M4平垫；轴水平X；穿木板φ4.5后入抱角焊母；订单具体SKU、包装量和库存待采购核对。
H18 | 承托盒M4焊接螺母 | S09C | 采购五金 | 可焊钢本色 |  | 8 | 只 | 8 | M4×0.7；对边9；厚3.5；定位凸台5.97最大 |  | 外购成品；按型号采购并做首件配装 | H02 | 50 | 准确规格商品/可选规格页可网购；中国配送及实时库存未核 | 采购数量 | https://www.nufast.co.uk/uploads/DIN_929.pdf | DIN929 M4 钢本色；T2抱角φ6 H11定位焊；与M4×25配套；订单具体SKU、包装量和库存待采购核对。
H19 | 翻盖独立承托角码 | A03 | 采购五金 | SUS304 |  | 8 | 只 | 8 | 30×30×宽12×T2.5；4×φ3.5沉φ6.5；两面孔距直角基准11/24 |  | 外购成品；按型号采购并做首件配装 | H03 | 51 | 成品或标准件可订购；未下单、实时库存未核 | 采购数量 | https://global.sugatsune.com/cn/zh-cn/arch/products/22735_a | SU-30S / 120-030-070；每盖两短端各1只；角码钢顶Z882−实测含胶软垫厚（名义879.77）；X450..480/720..750及+800；Y中心552/648；厂家安装目录配长螺钉会穿T15板，本项目另购φ3×12；水平面不锁翻盖。
H20 | 角码木螺钉 | A03 | 采购五金 | 镀锌钢 |  | 16 | 只 | 16 | 每角码竖面2只；杆φ3、长12 |  | 外购成品；按型号采购并做首件配装 | H03 | 51 | 准确规格商品/可选规格页可网购；中国配送及实时库存未核 | 采购数量 | https://www.misumi.com.cn/ | WV007880 / φ3×12沉头TX10；经T2.5角码横向入T15板约9.5；预钻孔径按实际木料试样，深度限位；订单具体SKU、包装量和库存待采购核对。
H21 | 角码软垫 | A03 | 采购五金 | EPDM橡胶 |  | 8 | 片 | 8 | 实心EPDM片200×300×T2，胶另约0.22~0.24；裁8片24×12 |  | 外购成品；按型号采购并做首件配装 | H03 | 51 | 德国厂家网店可下单1片；国内配送和库存未核 | 采购数量 | https://www.fugendichtband24.de/EPDM-Vollgummimatte-2mm-Staerke-200mm-x-300mm-einseitig-selbstklebend-ca-65-Shore-A.htm | 100191 / EAN4260627935185；含胶名义2.23；按实测总厚定位角码钢顶Z882−实测厚，使软垫顶882；Shore A约65；每桌切8片净面积2304mm²；1片原板足够。含胶厚必须到货实测。
B01 | 成品毛刷条 | A03 | 采购五金 | 尼龙毛＋铝座 |  | 2 | 根 | 2 | 每根1000；尼龙毛长19；F型铝座；截面总26.5、座6.7×6.7 |  | 外购成品；按型号采购并做首件配装 | H01 | 49 | 成品或标准件可订购；未下单、实时库存未核 | 采购数量 | https://uk.rs-online.com/web/p/door-seals/3269808 | RS PRO 326-9808；切160+298+500+298+160=1416；4处1缝合计覆盖1420；低Y侧28×7槽，刷毛向+Y，尖端留1；两个298段随W02A翻盖，其余3段固定W01；采购2m含584mm下料余量；取消不明B02挡条。
B03 | 毛刷固定木螺钉 | A03 | 采购五金 | 304不锈钢黑色 |  | 10 | 只 | 10 | 每毛刷段2枚；5段共10枚 |  | 外购成品；按型号采购并做首件配装 | H01 | 49 | 准确规格商品/可选规格页可网购；中国配送及实时库存未核 | 采购数量 | https://www.misumi.com.cn/ | 000338aa230623qmaneu / φ3×8；成品铝型材自配φ3.5孔；不得把型材截面剪短；木板槽后余厚11，限深避免穿面；订单具体SKU、包装量和库存待采购核对。
H22 | 横梁调整垫片 | S09A | 采购五金 | SUS304 |  | 64 | 片 | 64 | 内径6、外径12、厚1；每个螺栓4片叠为4 |  | 外购成品；按型号采购并做首件配装 | H02 | 50 | 厂家网店100片/包可加入购物车；国内配送和库存未核 | 采购数量 | https://www.wkooa.com/product/6x12x1-shim-washers-stainless-steel-round-metric-din988-w29338 | W29338 / DIN988 6×12×1；16个M6螺栓位置×4片=64；每端2螺栓8片；使478总长梁装入486内净距；成品调整片，不能按8个梁端误计32；安装实测总厚及孔径通过性。
H23 | 检修盖及吊板防坠索 | A04 | 采购五金 | 不锈钢素色 |  | 4 | 根 | 4 | 钢索φ1.6；索环根间150；两端片孔φ5.3、宽14、T1.5；拉直孔心距约183 |  | 外购成品；按型号采购并做首件配装 | H01 | 49 | 经销网店可加入购物篮但页面无现货；须核交期及中国配送 | 采购数量 | https://www.ganternorm.com/en/products/3.2-Mounting-Positioning-Leveling-with-Retaining-Cables-Screws-Clamping-and-Supporting-Elements/Retaining-cables/GN-111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 | GN111.2-150-C-BL；盖2根、吊板2根；载板平差X40/Y20、初始Z差2，下放约175.45；盖竖挂平差10、上下差182.73；有效长度按实物核；厂家1800N是静载参考，非动态跌落额定。固定端片两面大垫夹持，盖/吊板下放全过程托住，防坠仅兜底。
H24 | 防坠索端片紧固配套 | A04 | 采购五金 | A2不锈钢 |  | 8 | 套 | 8 | 每套1盘头螺钉、2大垫φ4.3×12×T1、1防松母；M4母总高5 |  | 外购成品；按型号采购并做首件配装 | H01 | 49 | 螺钉准确型号可网购；套内垫圈与螺母分购，国内配送及库存未核 | 采购数量 | https://www.westfieldfasteners.co.uk/Standards/Washer-od3nom-M.pdf | ISO7045 M4×16＋2×DIN9021 M4＋DIN985 M4；悬臂螺钉从上向下，头＋上垫最大4.25；端片直接贴钢件下侧，下垫及防松母夹紧；木底净0.75；悬臂T3＋两垫T1＋端片T1.5＋防松母高5，M4×16末端余4.5；已核下方不撞梁/箱体。盖锚(860/1140,440)，底盘锚同X、Y400。
A06 | 成品护口与孔盖组件 | A03 | 装配 | 锌合金衬套＋塑料盖组合 |  | 1 | 套 | 1 | 20只衬套＋10只盖 |  | 成品安装与首件卡紧复核 | A06 | 52 | 首件跨品牌配装待核 | 装配数量；材料按子件领用 | H25/H26厂家尺寸及W01孔位 | 成品H25/H26替代R01机加工M01/M02/M03；装配计数不叠加采购子件。

Sheet: 图纸目录
图纸目录
HW73005-L2000 L2000体验桌 R03 尺寸单位 mm
批量（套） | 1 |  | 版次日期 | 2026-10-01
PDF 页码指本次交付图纸文件内的页序；零件编号与清单、图号对应。
图号 | 图纸名称 | PDF 页 | 比例 | 关联零件 / 总成 | 状态 | 内容说明 | 依据
I01 | 件号索引 · 总成与制作件 | 1 | 1:1 | A01、A04、A03、A05、W01、W02A、W02B、W03、W03A、W04B、W05、S01、S02、A07、S03A、S03B、S03C、S04、S07、S05、S06、A08、S08、S08A、S09A、S09B、S09C、S10A、S10B、S10C、S10D、S10E、A06 | 件号双向索引
I02 | 件号索引 · 成品五金 | 2 | 1:1 | H01、H02、H03、H04、H05、H06、H07、H09、H10、H11、H12、H13、H25、H26、H14、H15、H16、H17、H18、H19、H20、H21、B01、B03、H22、H23、H24 | 件号双向索引
I03 | 件号索引 · 电气与孔路线 | 3 | 1:1 | E01、E02、E03、E04、E05、E06、E07、E08、E09、E10、E11、E12、E13、E14、E15、E16、E17、E18、E19、E20、E21、E22、E23、E24 | 件号双向索引
A01 | 整桌总装 · 三视、基准与装配尺寸 | 4 | 1:10 | A01 | 三视已绘 | 整桌总装 · 三视、基准与装配尺寸 | 顾客DWG SRC-02/03/04 + R02装配控制
A02 | 整桌分层装配 · 先看各件在哪里 | 5 | 轴测示意 | S01、S02、S03A、S04、S05、S07、S08A、S10A、S10B、W01、W02A、W02B、W03、W03A、W04B、W05 | 同源三维装配定位
V02 | 桌面组件 · 翻盖与过线口 | 6 | 轴测示意 | B01、B03、H07、H25、H26、W01、W02A、W02B | 同源三维装配定位
V10 | 木盒组件 · 出线口、承托角与盒底 | 7 | 轴测示意 | H06、H19、H20、H21、W03、W03A、W04B、W05 | 同源三维装配定位
V03 | 钢架组件 · 梁、固定耳与四只桌腿 | 8 | 轴测示意 | S01、S02、S03A、S03B、S03C、S05、S06、S08A、S09A、S09B、S09C | 同源三维装配定位
V04 | 检修组件 · 门盖与中央下放组件 | 9 | 轴测示意 | H03、H04、H13、H14、H23、H24、S04、S07、S10A、S10B、S10C、S10D、S10E | 同源三维装配定位
V05 | 连接五金 · 四类局部安装 | 10 | 局部轴测示意 | H09、H10、H11、H15、H16、H17、H18、H19、H20、H21、H22、S05、S09A、S09B、S09C、W01、W04B | 同源模型局部安装
V06 | 电器位置 · 钢架内安装位置 | 11 | 轴测示意 | E01、E02、E03、E07、E08、E09、S01、S02、S04、S05、S08A | 同源三维装配定位
V07 | 门与脚五金 · 四类局部安装 | 12 | 局部轴测示意 | E02、H01、H02、H03、H04、H05、H12、S03C、S04、S07、S10E | 同源模型局部安装
V08 | 分线盒内部 · 从下方看接线操作面 | 13 | 轴测示意 | E06、E07、E11、E12、E13、E14、E15 | 同源三维装配定位
V09 | 电气连接件 · 入口与接地局部 | 14 | 局部轴测示意 | E09、E10、E16、E17、E18、E19、E20、E22、E23、E24、S04、S08A、S10A、S10B | 同源模型局部安装
D01 | D01 桌面可拆固定 · M6嵌件节点、工具柱及拆卸顺序 | 15 | 2:1 | W01、S09B、H09 | 三视与检修路径已绘；未经承载验算或生产放行 | 真实厚度链、嵌件盲孔控制与完整桌面拆卸动作 | R02用户要求；保留R01外包、C筋与承托盒；新增服务结构
S10F | S10F 中央检修服务位 · 成品索长度、独立锚点及实体行程 | 16 | 1:3 | S10A、S10B、S10C、H23、H24 | 三视与检修路径已绘；未经承载验算或生产放行 | 闭合/服务实体位置与成品双端片索的三维长度闭合 | R02用户要求；保留R01外包、C筋与承托盒；新增服务结构
A04 | 钢结构总成 · 底视布置、三视与焊接 | 17 | 1:10 | A04 | 三视已绘 | 钢结构总成 · 底视布置、三视与焊接 | 顾客DWG SRC-02/03/04 + R02装配控制
A03 | 桌面与翻盖总成｜孔位、毛刷及护口布置 | 18 | 1:10 | A03 | 成型三视已绘；配孔及装配按页内说明 | 桌面与翻盖总成｜孔位、毛刷及护口布置 | 原图总装顶视及D节点；R02成品五金与可拆固定修订
A05 | 承托盒总成｜长侧出线、短侧固定 | 19 | 1:2 | A05 | 成型三视已绘；配孔及装配按页内说明 | 承托盒总成｜长侧出线、短侧固定 | 原图总装顶视及D节点；R02成品五金与可拆固定修订
W01 | W01 桌面成品板｜实际切口与封边控制 | 20 | 1:10 | W01 | 成型三视已绘；配孔及装配按页内说明 | W01 桌面成品板｜实际切口与封边控制 | 原图总装顶视及D节点；R02成品五金与可拆固定修订
W02 | W02A / W02B 翻盖板｜有槽与实板配对 | 21 | 1:2 | W02A、W02B | 成型三视已绘；配孔及装配按页内说明 | W02A / W02B 翻盖板｜有槽与实板配对 | 原图总装顶视及D节点；R02成品五金与可拆固定修订
W03 | W03 / W03A 承托盒长侧板｜无孔与有孔 | 22 | 1:2 | W03、W03A | 成型三视已绘；配孔及装配按页内说明 | W03 / W03A 承托盒长侧板｜无孔与有孔 | 原图总装顶视及D节点；R02成品五金与可拆固定修订
W04 | W04B 承托盒短侧板｜固定孔与承托预孔 | 23 | 1:2 | W04B | 成型三视已绘；配孔及装配按页内说明 | W04B 承托盒短侧板｜固定孔与承托预孔 | 原图总装顶视及D节点；R02成品五金与可拆固定修订
W05 | W05 承托盒底板｜托底构造与三视 | 24 | 1:2 | W05 | 成型三视已绘；配孔及装配按页内说明 | W05 承托盒底板｜托底构造与三视 | 原图总装顶视及D节点；R02成品五金与可拆固定修订
D02 | 翻盖与成品毛刷安装 · 顶装桶铰链、承托及分段 | 25 | 1:1 | W01、W02A、W02B | 成型三视已绘；配孔及装配按页内说明 | 翻盖与成品毛刷安装 · 顶装桶铰链、承托及分段 | 原图总装顶视及D节点；R02成品五金与可拆固定修订
S01 | 长边斜腹板 · 成型与端部放样 | 26 | 1:10 | S01 | 已绘成型尺寸及工艺说明 | 长边斜腹板 · 成型与端部放样 | 顾客DWG SRC-02/03/04；R01深化
S02 | 短边斜腹板 · 成型与端部放样 | 27 | 1:5 | S02 | 已绘成型尺寸及工艺说明 | 短边斜腹板 · 成型与端部放样 | 顾客DWG SRC-02/03/04；R01深化
A07 | 刀形桌腿总成 · 分缝与成品脚件 | 28 | 1:5 | A07 | 已绘成型尺寸及工艺说明 | 刀形桌腿总成 · 分缝与成品脚件 | 顾客DWG SRC-02/03/04；R01深化
S03A | 刀形腿壳 · 成型三视与焊缝 | 29 | 1:5 | S03A | 已绘成型尺寸及工艺说明 | 刀形腿壳 · 成型三视与焊缝 | 顾客DWG SRC-02/03/04；R01深化
S03BC | 刀形腿封板 · 内端板与底封板 | 30 | 1:5 | S03B、S03C | 已绘成型尺寸及工艺说明 | 刀形腿封板 · 内端板与底封板 | 顾客DWG SRC-02/03/04；R01深化
S04 | 桌肚底盘 · 折边、检修口与定位 | 31 | 1:10 | S04 | 已绘成型尺寸及工艺说明 | 桌肚底盘 · 折边、检修口与定位 | 顾客DWG SRC-02/03/04；R01深化
S07 | 检修门 · 门缝、铰链与排插固定 | 32 | 1:5 | S07 | 已绘成型尺寸及工艺说明 | 检修门 · 门缝、铰链与排插固定 | 顾客DWG SRC-02/03/04；R01深化
S05 | S05 长向 C 型加强筋成型制作 | 33 | 1:5 | S05 | 成型已绘；干涉按同版腹板已消除；试装与折弯展开待核 | 长向C筋成型三视、原端部斜切控制与安装横截面；T2、30×97、唇13、净430。 | 源BV-BV 0x7EC7..0x7EF2；D节点0x84A2..0x84D5；R01包络与筋距统一
S06 | S06 U 型卡槽成型制作与安装 | 34 | 1:1 | S06 | 成型已绘；试卡与折弯展开待核 | U槽成型三视与口沿截面；真实底宽25、喉口18、高20，外翻唇单独表达。 | 源U型卡槽0xD353..0xD35F及18/20/25/100标注；R01按T1归整
A08 | 内部加强与检修 · 八点拆面、横向框架及接近通道 | 35 | 1:10 | A08 | 三视与检修路径已绘；未经承载验算或生产放行 | 原结构内补横向框架、可达八点拆面与中央检修路径 | R02用户要求；保留R01外包、C筋与承托盒；新增服务结构
S08 | S08 可拆横梁总成 / S08A 矩管身 · 成型三视与端接口 | 36 | 1:2 | S08、S08A | 三视与检修路径已绘；未经承载验算或生产放行 | 可拆横梁及管身三视、长度链和C腔连接坐标 | R02用户要求；保留R01外包、C筋与承托盒；新增服务结构
S09A | S09A 横梁端板 · 焊母接口及C腹板连接 | 37 | 1:1 | S09A | 三视与检修路径已绘；未经承载验算或生产放行 | 端板真实三视、两孔定位与焊母先装顺序 | R02用户要求；保留R01外包、C筋与承托盒；新增服务结构
S09B | S09B 桌面固定耳 · 原检修口上方八点可拆接口 | 38 | 1:1 | S09B | 三视与检修路径已绘；未经承载验算或生产放行 | 八点固定耳三视与实际工具入口位置 | R02用户要求；保留R01外包、C筋与承托盒；新增服务结构
S09C | S09C 承托盒抱角 · 盒固定在钢架且可拆 | 39 | 1:1 | S09C | 三视与检修路径已绘；未经承载验算或生产放行 | 左右抱角分别三视、底托和水平紧固孔坐标 | R02用户要求；保留R01外包、C筋与承托盒；新增服务结构
S10 | S10 中央检修盖与吊检修板 · 三视、支承及防坠 | 40 | 1:2 | S10A、S10B | 三视与检修路径已绘；未经承载验算或生产放行 | 中央盖与载盒检修板分别三视；明确实际支承和下放动作 | R02用户要求；保留R01外包、C筋与承托盒；新增服务结构
S10C | S10C 检修板悬臂 · 左右转向装配、焊母及防坠锚点 | 41 | 1:1 | S10C | 三视与检修路径已绘；未经承载验算或生产放行 | 悬臂三视、四处实体支承与下放吊线锚点 | R02用户要求；保留R01外包、C筋与承托盒；新增服务结构
S10DE | S10D 补强片 / S10E 锁接收座 · 成型三视与接触剖面 | 42 | 1:1 | S10D、S10E | 三视与检修路径已绘；未经承载验算或生产放行 | 中央盖补强片及两锁座分别三视，明确可制造形体和接触界面 | R02用户要求；保留R01外包、C筋与承托盒；新增服务结构
E01 | 电气装配导航｜先定位，再按线路号穿孔 | 43 | 1:10 | E03、E04、E08 | 图形与接口导航；到货/实装/保护验收未放行 | 电气装配导航｜先定位，再按线路号穿孔 | R03 routes.json，R02证据及R03孔端安装布置
E02 | 五路电气原理｜按L / N / PE分线，圆点才相连 | 44 | 1:10 |  | 图形与接口导航；到货/实装/保护验收未放行 | 五路电气原理｜按L / N / PE分线，圆点才相连 | R03 routes.json，R02证据及R03孔端安装布置
E03 | 中央端子装配｜从端子编号找到支路与检修步骤 | 45 | 1:1 | E06、E11、E12、E13、E14、E15、E16、E21、E22、E23、E24 | 图形与接口导航；到货/实装/保护验收未放行 | 中央端子装配｜从端子编号找到支路与检修步骤 | R03 routes.json，R02证据及R03孔端安装布置
E04 | 入口与中央盒｜找孔号，再装护口和抗拉固定 | 46 | 1:1 | E07、E09、E10、E17、E18、E19、E20 | 图形与接口导航；到货/实装/保护验收未放行 | 入口与中央盒｜找孔号，再装护口和抗拉固定 | R03 routes.json，R02证据及R03孔端安装布置
E05 | 近门与远门｜W3 / W4分别穿两只C筋护口 | 47 | 1:3 | E02、E05 | 图形与接口导航；到货/实装/保护验收未放行 | 近门与远门｜W3 / W4分别穿两只C筋护口 | R03 routes.json，R02证据及R03孔端安装布置
E06 | 木盒与桌面｜原装线走长边孔，用户线走桌面预留孔 | 48 | 1:3 | E01 | 图形与接口导航；到货/实装/保护验收未放行 | 木盒与桌面｜原装线走长边孔，用户线走桌面预留孔 | R03 routes.json，R02证据及R03孔端安装布置
H01 | H01 成品五金｜型号、数量与接口索引 | 49 | 1:1 | H05、H06、B01、B03、H23、H24 | 接口已绘；到货及首件配装待核 | 成品型号、数量和接口导航；包装量见完整采购表。 | 厂家公开尺寸图＋R02结构接口；链接见采购来源清单
H02 | H02 桌面、调节脚及防脱紧固接口 | 50 | 2:1 | H01、H02、H09、H10、H11、H13、H14、H15、H16、H17、H18、H22 | 接口已绘；到货及首件配装待核 | 8点可拆桌面、8只薄脚、4点盖和4点吊板防脱的实际厚度堆叠与螺纹啮合。 | 厂家公开尺寸图＋R02结构接口；链接见采购来源清单
H03 | H03 检修门、工具锁与小翻盖安装接口 | 51 | 1:1 | H03、H04、H07、H12、H19、H20、H21 | 接口已绘；到货及首件配装待核 | 可抽轴门合页开孔、转舌锁开孔/接收高度、桶铰顶装及翻盖独立承托。 | 厂家公开尺寸图＋R02结构接口；链接见采购来源清单
A06 | A06 成品小孔衬套与闲置孔盖装配接口 | 52 | 2:1 | A06、H25、H26 | 接口已绘；到货及首件配装待核 | 外购CHC-S18BL替代原机加工护套；φ14安装孔与φ12盖配合、法兰高度控制。 | 厂家公开尺寸图＋R02结构接口；链接见采购来源清单

Sheet: 三视覆盖
整机、总成与零件三视覆盖
HW73005-L2000 L2000体验桌 R03 尺寸单位 mm
批量（套） | 1 |  | 版次日期 | 2026-10-01
已提供表示图中存在相应视图，尺寸和工艺完整性另见状态与复核记录；未给出映射的视图保持待核实。
对象编号 | 对象名称 | 对象类型 | 对应图号 | PDF 页 | 正视图 | 俯视图 | 侧视图 | 状态 | 所属 / 关联对象 | 说明
I01 | 件号索引 · 总成与制作件 | 图纸 / 总成 | I01 | 1 | 索引 | 索引 | 索引 | 件号双向索引 | A01、A04、A03、A05、W01、W02A、W02B、W03、W03A、W04B、W05、S01、S02、A07、S03A、S03B、S03C、S04、S07、S05、S06、A08、S08、S08A、S09A、S09B、S09C、S10A、S10B、S10C、S10D、S10E、A06
I02 | 件号索引 · 成品五金 | 图纸 / 总成 | I02 | 2 | 索引 | 索引 | 索引 | 件号双向索引 | H01、H02、H03、H04、H05、H06、H07、H09、H10、H11、H12、H13、H25、H26、H14、H15、H16、H17、H18、H19、H20、H21、B01、B03、H22、H23、H24
I03 | 件号索引 · 电气与孔路线 | 图纸 / 总成 | I03 | 3 | 索引 | 索引 | 索引 | 件号双向索引 | E01、E02、E03、E04、E05、E06、E07、E08、E09、E10、E11、E12、E13、E14、E15、E16、E17、E18、E19、E20、E21、E22、E23、E24
A01 | 整桌总装 · 三视、基准与装配尺寸 | 图纸 / 总成 | A01 | 4 | 已绘 | 已绘 | 已绘 | 三视已绘 | A01 | 整桌总装 · 三视、基准与装配尺寸
A02 | 整桌分层装配 · 先看各件在哪里 | 图纸 / 总成 | A02 | 5 | 参见对应制作图 | 参见对应制作图 | 参见对应制作图 | 同源三维装配定位 | S01、S02、S03A、S04、S05、S07、S08A、S10A、S10B、W01、W02A、W02B、W03、W03A、W04B、W05
V02 | 桌面组件 · 翻盖与过线口 | 图纸 / 总成 | V02 | 6 | 参见对应制作图 | 参见对应制作图 | 参见对应制作图 | 同源三维装配定位 | B01、B03、H07、H25、H26、W01、W02A、W02B
V10 | 木盒组件 · 出线口、承托角与盒底 | 图纸 / 总成 | V10 | 7 | 参见对应制作图 | 参见对应制作图 | 参见对应制作图 | 同源三维装配定位 | H06、H19、H20、H21、W03、W03A、W04B、W05
V03 | 钢架组件 · 梁、固定耳与四只桌腿 | 图纸 / 总成 | V03 | 8 | 参见对应制作图 | 参见对应制作图 | 参见对应制作图 | 同源三维装配定位 | S01、S02、S03A、S03B、S03C、S05、S06、S08A、S09A、S09B、S09C
V04 | 检修组件 · 门盖与中央下放组件 | 图纸 / 总成 | V04 | 9 | 参见对应制作图 | 参见对应制作图 | 参见对应制作图 | 同源三维装配定位 | H03、H04、H13、H14、H23、H24、S04、S07、S10A、S10B、S10C、S10D、S10E
V05 | 连接五金 · 四类局部安装 | 图纸 / 总成 | V05 | 10 | 对应制作/接口图 | 对应制作/接口图 | 对应制作/接口图 | 同源模型局部安装 | H09、H10、H11、H15、H16、H17、H18、H19、H20、H21、H22、S05、S09A、S09B、S09C、W01、W04B
V06 | 电器位置 · 钢架内安装位置 | 图纸 / 总成 | V06 | 11 | 参见对应制作图 | 参见对应制作图 | 参见对应制作图 | 同源三维装配定位 | E01、E02、E03、E07、E08、E09、S01、S02、S04、S05、S08A
V07 | 门与脚五金 · 四类局部安装 | 图纸 / 总成 | V07 | 12 | 对应制作/接口图 | 对应制作/接口图 | 对应制作/接口图 | 同源模型局部安装 | E02、H01、H02、H03、H04、H05、H12、S03C、S04、S07、S10E
V08 | 分线盒内部 · 从下方看接线操作面 | 图纸 / 总成 | V08 | 13 | 参见对应制作图 | 参见对应制作图 | 参见对应制作图 | 同源三维装配定位 | E06、E07、E11、E12、E13、E14、E15
V09 | 电气连接件 · 入口与接地局部 | 图纸 / 总成 | V09 | 14 | 对应制作/接口图 | 对应制作/接口图 | 对应制作/接口图 | 同源模型局部安装 | E09、E10、E16、E17、E18、E19、E20、E22、E23、E24、S04、S08A、S10A、S10B
D01 | D01 桌面可拆固定 · M6嵌件节点、工具柱及拆卸顺序 | 图纸 / 总成 | D01 | 15 | D01/正视 | D01/俯视 | D01/右视 | 三视与检修路径已绘；未经承载验算或生产放行 | W01、S09B、H09 | 真实厚度链、嵌件盲孔控制与完整桌面拆卸动作
S10F | S10F 中央检修服务位 · 成品索长度、独立锚点及实体行程 | 图纸 / 总成 | S10F | 16 | S10F/正视 | S10F/俯视 | S10F/右视 | 三视与检修路径已绘；未经承载验算或生产放行 | S10A、S10B、S10C、H23、H24 | 闭合/服务实体位置与成品双端片索的三维长度闭合
A04 | 钢结构总成 · 底视布置、三视与焊接 | 图纸 / 总成 | A04 | 17 | 已绘 | 已绘 | 已绘 | 三视已绘 | A04 | 钢结构总成 · 底视布置、三视与焊接
A03 | 桌面与翻盖总成｜孔位、毛刷及护口布置 | 图纸 / 总成 | A03 | 18 | A03/正视：实体及尺寸已绘 | A03/俯视：实体及孔槽已绘 | A03/右视：实体、厚度及隐藏线已绘 | 成型三视已绘；配孔及装配按页内说明 | A03 | 桌面与翻盖总成｜孔位、毛刷及护口布置
A05 | 承托盒总成｜长侧出线、短侧固定 | 图纸 / 总成 | A05 | 19 | A05/正视：实体及尺寸已绘 | A05/俯视：实体及孔槽已绘 | A05/右视：实体、厚度及隐藏线已绘 | 成型三视已绘；配孔及装配按页内说明 | A05 | 承托盒总成｜长侧出线、短侧固定
W01 | W01 桌面成品板｜实际切口与封边控制 | 图纸 / 总成 | W01 | 20 | W01/正视：实体及尺寸已绘 | W01/俯视：实体及孔槽已绘 | W01/右视：实体、厚度及隐藏线已绘 | 成型三视已绘；配孔及装配按页内说明 | W01 | W01 桌面成品板｜实际切口与封边控制
W02 | W02A / W02B 翻盖板｜有槽与实板配对 | 图纸 / 总成 | W02 | 21 | W02/正视：实体及尺寸已绘 | W02/俯视：实体及孔槽已绘 | W02/右视：实体、厚度及隐藏线已绘 | 成型三视已绘；配孔及装配按页内说明 | W02A、W02B | W02A / W02B 翻盖板｜有槽与实板配对
W03 | W03 / W03A 承托盒长侧板｜无孔与有孔 | 图纸 / 总成 | W03 | 22 | W03/正视：实体及尺寸已绘 | W03/俯视：实体及孔槽已绘 | W03/右视：实体、厚度及隐藏线已绘 | 成型三视已绘；配孔及装配按页内说明 | W03、W03A | W03 / W03A 承托盒长侧板｜无孔与有孔
W04 | W04B 承托盒短侧板｜固定孔与承托预孔 | 图纸 / 总成 | W04 | 23 | W04/正视：实体及尺寸已绘 | W04/俯视：实体及孔槽已绘 | W04/右视：实体、厚度及隐藏线已绘 | 成型三视已绘；配孔及装配按页内说明 | W04B | W04B 承托盒短侧板｜固定孔与承托预孔
W05 | W05 承托盒底板｜托底构造与三视 | 图纸 / 总成 | W05 | 24 | W05/正视：实体及尺寸已绘 | W05/俯视：实体及孔槽已绘 | W05/右视：实体、厚度及隐藏线已绘 | 成型三视已绘；配孔及装配按页内说明 | W05 | W05 承托盒底板｜托底构造与三视
D02 | 翻盖与成品毛刷安装 · 顶装桶铰链、承托及分段 | 图纸 / 总成 | D02 | 25 | 安装节点剖面 | 五段毛刷坐标表 | 成品支承安装坐标；非零件制作页 | 成型三视已绘；配孔及装配按页内说明 | W01、W02A、W02B | 翻盖与成品毛刷安装 · 顶装桶铰链、承托及分段
S01 | 长边斜腹板 · 成型与端部放样 | 图纸 / 总成 | S01 | 26 | 已绘正视 | 已绘俯视 | 已绘右视 | 已绘成型尺寸及工艺说明 | S01 | 长边斜腹板 · 成型与端部放样
S02 | 短边斜腹板 · 成型与端部放样 | 图纸 / 总成 | S02 | 27 | 已绘正视 | 已绘俯视 | 已绘右视 | 已绘成型尺寸及工艺说明 | S02 | 短边斜腹板 · 成型与端部放样
A07 | 刀形桌腿总成 · 分缝与成品脚件 | 图纸 / 总成 | A07 | 28 | 已绘正视 | 已绘俯视 | 已绘右视 | 已绘成型尺寸及工艺说明 | A07 | 刀形桌腿总成 · 分缝与成品脚件
S03A | 刀形腿壳 · 成型三视与焊缝 | 图纸 / 总成 | S03A | 29 | 已绘正视 | 已绘俯视 | 已绘右视 | 已绘成型尺寸及工艺说明 | S03A | 刀形腿壳 · 成型三视与焊缝
S03BC | 刀形腿封板 · 内端板与底封板 | 图纸 / 总成 | S03BC | 30 | 已绘正视 | 已绘俯视 | 已绘右视 | 已绘成型尺寸及工艺说明 | S03B、S03C | 刀形腿封板 · 内端板与底封板
S04 | 桌肚底盘 · 折边、检修口与定位 | 图纸 / 总成 | S04 | 31 | 已绘正视 | 已绘俯视 | 已绘右视 | 已绘成型尺寸及工艺说明 | S04 | 桌肚底盘 · 折边、检修口与定位
S07 | 检修门 · 门缝、铰链与排插固定 | 图纸 / 总成 | S07 | 32 | 已绘正视 | 已绘俯视 | 已绘右视 | 已绘成型尺寸及工艺说明 | S07 | 检修门 · 门缝、铰链与排插固定
S05 | S05 长向 C 型加强筋成型制作 | 图纸 / 总成 | S05 | 33 | S05 正视图 | S05 俯视图 | S05 右视图 | 成型已绘；干涉按同版腹板已消除；试装与折弯展开待核 | S05 | 长向C筋成型三视、原端部斜切控制与安装横截面；T2、30×97、唇13、净430。
S06 | S06 U 型卡槽成型制作与安装 | 图纸 / 总成 | S06 | 34 | S06 正视图 | S06 俯视图 | S06 右视图 | 成型已绘；试卡与折弯展开待核 | S06 | U槽成型三视与口沿截面；真实底宽25、喉口18、高20，外翻唇单独表达。
A08 | 内部加强与检修 · 八点拆面、横向框架及接近通道 | 图纸 / 总成 | A08 | 35 | A08/正视 | A08/俯视 | A08/右视 | 三视与检修路径已绘；未经承载验算或生产放行 | A08 | 原结构内补横向框架、可达八点拆面与中央检修路径
S08 | S08 可拆横梁总成 / S08A 矩管身 · 成型三视与端接口 | 图纸 / 总成 | S08 | 36 | S08/正视 | S08/俯视 | S08/右视 | 三视与检修路径已绘；未经承载验算或生产放行 | S08、S08A | 可拆横梁及管身三视、长度链和C腔连接坐标
S09A | S09A 横梁端板 · 焊母接口及C腹板连接 | 图纸 / 总成 | S09A | 37 | S09A/正视 | S09A/俯视 | S09A/右视 | 三视与检修路径已绘；未经承载验算或生产放行 | S09A | 端板真实三视、两孔定位与焊母先装顺序
S09B | S09B 桌面固定耳 · 原检修口上方八点可拆接口 | 图纸 / 总成 | S09B | 38 | S09B/正视 | S09B/俯视 | S09B/右视 | 三视与检修路径已绘；未经承载验算或生产放行 | S09B | 八点固定耳三视与实际工具入口位置
S09C | S09C 承托盒抱角 · 盒固定在钢架且可拆 | 图纸 / 总成 | S09C | 39 | S09C/正视 | S09C/俯视 | S09C/右视 | 三视与检修路径已绘；未经承载验算或生产放行 | S09C | 左右抱角分别三视、底托和水平紧固孔坐标
S10 | S10 中央检修盖与吊检修板 · 三视、支承及防坠 | 图纸 / 总成 | S10 | 40 | S10/正视 | S10/俯视 | S10/右视 | 三视与检修路径已绘；未经承载验算或生产放行 | S10A、S10B | 中央盖与载盒检修板分别三视；明确实际支承和下放动作
S10C | S10C 检修板悬臂 · 左右转向装配、焊母及防坠锚点 | 图纸 / 总成 | S10C | 41 | S10C/正视 | S10C/俯视 | S10C/右视 | 三视与检修路径已绘；未经承载验算或生产放行 | S10C | 悬臂三视、四处实体支承与下放吊线锚点
S10DE | S10D 补强片 / S10E 锁接收座 · 成型三视与接触剖面 | 图纸 / 总成 | S10DE | 42 | S10DE/正视 | S10DE/俯视 | S10DE/右视 | 三视与检修路径已绘；未经承载验算或生产放行 | S10D、S10E | 中央盖补强片及两锁座分别三视，明确可制造形体和接触界面
E01 | 电气装配导航｜先定位，再按线路号穿孔 | 图纸 / 总成 | E01 | 43 | E01/正视安装投影 | E01/俯视安装投影 | E01/右视安装投影 | 图形与接口导航；到货/实装/保护验收未放行 | E03、E04、E08 | 电气装配导航｜先定位，再按线路号穿孔
E02 | 五路电气原理｜按L / N / PE分线，圆点才相连 | 图纸 / 总成 | E02 | 44 | E01/正视安装投影 | E01/俯视安装投影 | E01/右视安装投影 | 图形与接口导航；到货/实装/保护验收未放行 |  | 五路电气原理｜按L / N / PE分线，圆点才相连
E03 | 中央端子装配｜从端子编号找到支路与检修步骤 | 图纸 / 总成 | E03 | 45 | E01/正视安装投影 | E01/俯视安装投影 | E01/右视安装投影 | 图形与接口导航；到货/实装/保护验收未放行 | E06、E11、E12、E13、E14、E15、E16、E21、E22、E23、E24 | 中央端子装配｜从端子编号找到支路与检修步骤
E04 | 入口与中央盒｜找孔号，再装护口和抗拉固定 | 图纸 / 总成 | E04 | 46 | E01/正视安装投影 | E01/俯视安装投影 | E01/右视安装投影 | 图形与接口导航；到货/实装/保护验收未放行 | E07、E09、E10、E17、E18、E19、E20 | 入口与中央盒｜找孔号，再装护口和抗拉固定
E05 | 近门与远门｜W3 / W4分别穿两只C筋护口 | 图纸 / 总成 | E05 | 47 | E01/正视安装投影 | E01/俯视安装投影 | E01/右视安装投影 | 图形与接口导航；到货/实装/保护验收未放行 | E02、E05 | 近门与远门｜W3 / W4分别穿两只C筋护口
E06 | 木盒与桌面｜原装线走长边孔，用户线走桌面预留孔 | 图纸 / 总成 | E06 | 48 | E01/正视安装投影 | E01/俯视安装投影 | E01/右视安装投影 | 图形与接口导航；到货/实装/保护验收未放行 | E01 | 木盒与桌面｜原装线走长边孔，用户线走桌面预留孔
H01 | H01 成品五金｜型号、数量与接口索引 | 图纸 / 总成 | H01 | 49 | H01 购件索引 | H01 购件索引 | H01 购件索引 | 接口已绘；到货及首件配装待核 | H05、H06、B01、B03、H23、H24 | 成品型号、数量和接口导航；包装量见完整采购表。
H02 | H02 桌面、调节脚及防脱紧固接口 | 图纸 / 总成 | H02 | 50 | H02 安装剖面 | H02 安装接口 | H02 接口控制 | 接口已绘；到货及首件配装待核 | H01、H02、H09、H10、H11、H13、H14、H15、H16、H17、H18、H22 | 8点可拆桌面、8只薄脚、4点盖和4点吊板防脱的实际厚度堆叠与螺纹啮合。
H03 | H03 检修门、工具锁与小翻盖安装接口 | 图纸 / 总成 | H03 | 51 | H03 安装剖面 | H03 安装接口 | H03 接口控制 | 接口已绘；到货及首件配装待核 | H03、H04、H07、H12、H19、H20、H21 | 可抽轴门合页开孔、转舌锁开孔/接收高度、桶铰顶装及翻盖独立承托。
A06 | A06 成品小孔衬套与闲置孔盖装配接口 | 图纸 / 总成 | A06 | 52 | A06 轴向剖面 | A06 俯视图 | A06 轴对称右视 | 接口已绘；到货及首件配装待核 | A06、H25、H26 | 外购CHC-S18BL替代原机加工护套；φ14安装孔与φ12盖配合、法兰高度控制。
A01 | 体验桌总装 | 装配 | A01 | 4 | 本页正视 | 本页俯视 | 本页右视 | 图纸数字核对；实物首件未执行 | 整桌 | 总成数量不重复计入领料
A04 | 焊接钢结构总成 | 装配 | A04 | 17 | 本页正视 | 本页俯视 | 本页右视 | 图纸数字核对；实物首件未执行 | A01 | 总成数量不重复计入领料
A03 | 桌面翻盖总成 | 装配 | A03 | 18 | A03/正视/第18页 | A03/俯视/第18页 | A03/右视/第18页 | 成型三视已绘；五金安装按实物配孔 | A01 | 成品含封边；R02护口孔Ø14+0.5/0；底面八点M6嵌母，按D01定位。取消原12处木螺钉孔。
A05 | 翻盖承托盒总成 | 装配 | A05 | 19 | A05/正视/第19页 | A05/俯视/第19页 | A05/右视/第19页 | 成型三视已绘；五金安装按实物配孔 | A04 | 盒留钢架；W03A长侧φ50孔朝Y485，孔心Z842。
W01 | 桌面主板 | 木作 | W01 | 20 | W01/正视/第20页 | W01/俯视/第20页 | W01/右视/第20页 | 成型三视已绘；五金安装按实物配孔 | A03 | 成品含封边；R02护口孔Ø14+0.5/0；底面八点M6嵌母，按D01定位。取消原12处木螺钉孔。
W02A | 桌面有槽翻盖板 | 木作 | W02 | 21 | W02/正视/第21页 | W02/俯视/第21页 | W02/右视/第21页 | 成型三视已绘；五金安装按实物配孔 | A03 | 源D 0x8469…0x846e；R01长度298；安装在开口Y低值侧，槽口朝中央毛刷。
W02B | 桌面实截面翻盖板 | 木作 | W02 | 21 | W02/正视/第21页 | W02/俯视/第21页 | W02/右视/第21页 | 成型三视已绘；五金安装按实物配孔 | A03 | 源D 0x8465…0x8468；R01长度298；安装在开口Y高值侧，不复制A盖让位槽。
W03 | 承托盒长侧板（无孔） | 木作 | W03 | 22 | W03/正视/第22页 | W03/俯视/第22页 | W03/右视/第22页 | 成型三视已绘；五金安装按实物配孔 | A05 | 远侧Y700..715，每盒1片。
W03A | 承托盒长侧板（有孔） | 木作 | W03 | 22 | W03/正视/第22页 | W03/俯视/第22页 | W03/右视/第22页 | 成型三视已绘；五金安装按实物配孔 | A05 | 近侧Y485..500；孔心全局(600/1400,492.5,842)，孔朝-Y。
W04B | 承托盒短侧板 | 木作 | W04 | 23 | W04/正视/第23页 | W04/俯视/第23页 | W04/右视/第23页 | 成型三视已绘；五金安装按实物配孔 | A05 | 固定孔u25/175 v24；承托盲孔u52/148 v64.77/77.77。无过线孔。
W05 | 承托盒底板 | 木作 | W05 | 24 | W05/正视/第24页 | W05/俯视/第24页 | W05/右视/第24页 | 成型三视已绘；五金安装按实物配孔 | A05 | T5为源D节点实线归一结果；材质选用在R01声明。
S01 | 长边斜腹板 | 钣金 | S01 | 26 | 本页正视 | 本页俯视 | 本页右视 | 成型控制；展开补偿按设备首件 | A04 | 颜色、光泽、焊缝处理按样板；去毛刺、不得割手
S02 | 短边斜腹板 | 钣金 | S02 | 27 | 本页正视 | 本页俯视 | 本页右视 | 成型控制；展开补偿按设备首件 | A04 | 颜色、光泽、焊缝处理按样板；去毛刺、不得割手
A07 | 刀形桌腿焊接总成 | 装配 | A07 | 28 | 本页正视 | 本页俯视 | 本页右视 | R01分片与高度修正 | A04 | 颜色、光泽、焊缝处理按样板；去毛刺、不得割手
S03A | 刀形腿开口壳 | 钣金 | S03A | 29 | 本页正视 | 本页俯视 | 本页右视 | 成型控制；首件顶口放样 | A07 | 颜色、光泽、焊缝处理按样板；去毛刺、不得割手
S03B | 刀形腿内端封板 | 钣金 | S03BC | 30 | 本页正视 | 本页俯视 | 本页右视 | 成型控制；展开补偿按设备首件 | A07 | 颜色、光泽、焊缝处理按样板；去毛刺、不得割手
S03C | 刀形腿底封板 | 钣金 | S03BC | 30 | 本页正视 | 本页俯视 | 本页右视 | 配切件；按首件成型内腔 | A07 | 颜色、光泽、焊缝处理按样板；去毛刺、不得割手
S04 | 桌肚四边折边底盘 | 钣金 | S04 | 31 | 本页正视 | 本页俯视 | 本页右视 | R02门框、X0与中央口接口；展开按实际折弯补偿 | A04 | 颜色、光泽、焊缝处理按样板；去毛刺、不得割手
S07 | 桌肚检修门 | 钣金 | S07 | 32 | 本页正视 | 本页俯视 | 本页右视 | 成品型号孔图已纳入；到货同版复核 | A04 | 颜色、光泽、焊缝处理按样板；去毛刺、不得割手
S05 | 长向C型加强筋 | 钣金制造件 | S05 | 33 | S05 正视图 | S05 俯视图 | S05 右视图 | 成型已绘；工艺试制待核 | A04 | 每桌2根；唇边13，C口相向；净430/外跨490。端接口、折弯补偿与焊接收缩未放行。
S06 | U型卡槽 | 钣金制造件 | S06 | 34 | S06 正视图 | S06 俯视图 | S06 右视图 | 成型已绘；工艺试制待核 | A04 | 底宽不含外翻唇；中心(315.5,595)/(1674.5,595)，相距1359；先试卡，展开补偿待核。
A08 | 桌肚内部加强与检修总成 | 装配 | A08 | 35 | A08/正视 | A08/俯视 | A08/右视 | R02成型与检修包络；承载/连接强度/首件未验证 | A04 | 装配项不重复领料；首件与载荷待核
S08 | 可拆横梁焊接总成 | 装配 | S08 | 36 | S08/正视 | S08/俯视 | S08/右视 | R02成型与检修包络；承载/连接强度/首件未验证 | A08 | 4×M6/组；子件另计
S08A | 横梁矩管身 | 钣金制造件 | S08 | 36 | S08/正视 | S08/俯视 | S08/右视 | R02成型与检修包络；承载/连接强度/首件未验证 | S08 | 截面是初选；不能据此宣称承载通过
S09A | 可拆横梁端板 | 钣金制造件 | S09A | 37 | S09A/正视 | S09A/俯视 | S09A/右视 | R02成型与检修包络；承载/连接强度/首件未验证 | S08
S09B | 桌面M6固定耳 | 钣金制造件 | S09B | 38 | S09B/正视 | S09B/俯视 | S09B/右视 | R02成型与检修包络；承载/连接强度/首件未验证 | A08 | 顶面Z882；沿两C筋外侧焊接；旧木螺钉接口取消
S09C | 承托盒抱角 | 钣金制造件 | S09C | 39 | S09C/正视 | S09C/俯视 | S09C/右视 | R02成型与检修包络；承载/连接强度/首件未验证 | A08 | 同件左右各4；右向绕Z转180°装；M4从盒内拆装
S10A | 中央搭接检修盖 | 钣金制造件 | S10 | 40 | S10/正视 | S10/俯视 | S10/右视 | R02成型与检修包络；承载/连接强度/首件未验证 | A08 | 4防脱M5+2防坠线；卸下竖挂后露出窗口
S10B | 分线盒吊检修安装板 | 钣金制造件 | S10 | 40 | S10/正视 | S10/俯视 | S10/右视 | R02成型与检修包络；承载/连接强度/首件未验证 | A08 | 由S10C支承；盒孔依厂家模板；下放175.45；2独立吊线
S10C | 分线盒检修板悬臂 | 钣金制造件 | S10C | 41 | S10C/正视 | S10C/俯视 | S10C/右视 | R02成型与检修包络；承载/连接强度/首件未验证 | A08 | 同件左右转180°装；焊于邻梁；M5焊母另计
S10D | 中央盖M5焊母补强片 | 钣金制造件 | S10DE | 42 | S10DE/正视 | S10DE/俯视 | S10DE/右视 | R02成型与检修包络；承载/连接强度/首件未验证 | A08 | 焊在底盘内面；不改变1.5+1+2紧固叠层
S10E | 检修门锁接收槽形座 | 钣金制造件 | S10DE | 42 | S10DE/正视 | S10DE/俯视 | S10DE/右视 | R02成型与检修包络；承载/连接强度/首件未验证 | A08 | 接收面Z801.3；与锁舌0.2名义间隙、搭接10.4，须首件试扣
E01 | 桌面三位五孔+3USB排插 | 电气采购 | E06 | 48 | E01/安装正视投影 | E01/安装俯视投影 | E01/安装右视投影 | 数量与接口已定；产品适用认证/到货模板/实物验收待核 | A04 | 若需3USB-A须另选；厂家未给到货外包，实插净空待验
E02 | 桌肚八位五孔排插 | 电气采购 | E05 | 47 | E01/安装正视投影 | E01/安装俯视投影 | E01/安装右视投影 | 数量与接口已定；产品适用认证/到货模板/实物验收待核 | S07 | 门内验收包络400×100×86.5含固定器/插头；非厂家外形，须到货实插
E03 | 明装安全五孔插座 | 电气采购 | E01 | 43 | E01/安装正视投影 | E01/安装俯视投影 | E01/安装右视投影 | 数量与接口已定；产品适用认证/到货模板/实物验收待核 | A01 | 型号CCC、厂家接线图和外包待核，不锁定孔距
E04 | 三芯内部分支线束 | 电气辅材 | E01 | 43 | E01/安装正视投影 | E01/安装俯视投影 | E01/安装右视投影 | 长度待实测；未填0或估算领料 | A01 | W00外径≤8.5且厂家静态弯曲半径≤30；活动段另核；不剪改排插原线
E05 | 桌肚过线保护管 | 电气辅材 | E05 | 47 | E01/安装正视投影 | E01/安装俯视投影 | E01/安装右视投影 | 长度待实测；未填0或估算领料 | A01 | 源≥25管须核外径，DN25不等于外径25；不进入桌腿
E06 | 绝缘套管及线号配套 | 电气辅材 | E03 | 45 | E01/安装正视投影 | E01/安装俯视投影 | E01/安装右视投影 | 数量与接口已定；产品适用认证/到货模板/实物验收待核 | A01 | 仅附加绝缘；不得替代护套、护口或封闭接线盒
E07 | 中央成品分线盒与内板 | 电气采购 | E04 | 46 | E01/安装正视投影 | E01/安装俯视投影 | E01/安装右视投影 | 数量与接口已定；产品适用认证/到货模板/实物验收待核 | S10B | 箱200×200×70；另购内板182×182×2.05，不当作默认随箱；改孔后不宣称原IP68
E08 | 排插独立固定分支插座 | 电气采购 | E01 | 43 | E01/安装正视投影 | E01/安装俯视投影 | E01/安装右视投影 | 数量与接口已定；产品适用认证/到货模板/实物验收待核 | A01 | 不得用四位排插串接替代；外壳不任意钻孔
E09 | C14电源入口 | 电气采购 | E04 | 46 | E01/安装正视投影 | E01/安装俯视投影 | E01/安装右视投影 | 数量与接口已定；产品适用认证/到货模板/实物验收待核 | A01 | 后罩E18、快接E19、紧固E20分别计；中国适用认证待核
E10 | 国标10A/C13成品电源线 | 电气采购 | E04 | 46 | E01/安装正视投影 | E01/安装俯视投影 | E01/安装右视投影 | 数量与接口已定；产品适用认证/到货模板/实物验收待核 | A01 | 选定线径版本CCC与长度待核；不得剪改模压接头
E11 | L灰色直通端子 | 电气采购 | E03 | 45 | E01/安装正视投影 | E01/安装俯视投影 | E01/安装右视投影 | 数量与接口已定；产品适用认证/到货模板/实物验收待核 | A01 | 一夹一线；按厂家剥线10~12及压接工艺
E12 | N蓝色直通端子 | 电气采购 | E03 | 45 | E01/安装正视投影 | E01/安装俯视投影 | E01/安装右视投影 | 数量与接口已定；产品适用认证/到货模板/实物验收待核 | A01 | 严禁N-PE跨接；不得把单电位端子当多极
E13 | 黄绿PE端子 | 电气采购 | E03 | 45 | E01/安装正视投影 | E01/安装俯视投影 | E01/安装右视投影 | 数量与接口已定；产品适用认证/到货模板/实物验收待核 | A01 | XPE6接PE0，桌身/两门/中央组件独立跨接
E14 | 六位连续跨接桥 | 电气采购 | E03 | 45 | E01/安装正视投影 | E01/安装俯视投影 | E01/安装右视投影 | 数量与接口已定；产品适用认证/到货模板/实物验收待核 | A01 | 不得错购/020-000三对独立桥
E15 | 导轨端挡与绝缘端板 | 电气辅材 | E03 | 45 | E01/安装正视投影 | E01/安装俯视投影 | E01/安装右视投影 | 数量与接口已定；产品适用认证/到货模板/实物验收待核 | A01 | L/N/PE分区清晰；导轨保护接地和端子保持力待验
E16 | 金属件保护连接配套 | 电气辅材 | E03 | 45 | E01/安装正视投影 | E01/安装俯视投影 | E01/安装右视投影 | 数量与接口已定；产品适用认证/到货模板/实物验收待核 | A01 | 含M5×20焊柱/齿平垫/锁母各10及门M4套2；套管1；中央E21~24不重计
E17 | 进线与线束固定护口配套 | 电气辅材 | E04 | 46 | E01/安装正视投影 | E01/安装俯视投影 | E01/安装右视投影 | 数量与接口已定；产品适用认证/到货模板/实物验收待核 | A01 | X0独立夹护套；后罩/快接不抗拉；不破坏原装护套
E18 | C14原厂绝缘后罩 | 电气采购 | E04 | 46 | E01/安装正视投影 | E01/安装俯视投影 | E01/安装右视投影 | 数量与接口已定；产品适用认证/到货模板/实物验收待核 | A01 | 原厂适配6100-3；出线口内径8.5；装配后包络至Z834
E19 | 全绝缘快接母端 | 电气采购 | E04 | 46 | E01/安装正视投影 | E01/安装俯视投影 | E01/安装右视投影 | 数量与接口已定；产品适用认证/到货模板/实物验收待核 | A01 | 适1~1.5mm²、导体绝缘径≤3.3；按厂家拉脱/压接验收
E20 | C14入口固定紧固件 | 电气采购 | E04 | 46 | E01/安装正视投影 | E01/安装俯视投影 | E01/安装右视投影 | 数量与接口已定；产品适用认证/到货模板/实物验收待核 | A01 | 不作PE连接；实际板/法兰叠厚与突出量首件核定
E21 | 中央组件柔性PE线 | 电气采购 | E03 | 45 | E01/安装正视投影 | E01/安装俯视投影 | E01/安装右视投影 | 数量与接口已定；产品适用认证/到货模板/实物验收待核 | A01 | 各留≥250维护余量；载板下放175.45，盖索孔心距183，按S10F全程核定；不承担吊重
E22 | 中央PE移动端M4环端子 | 电气采购 | E03 | 45 | E01/安装正视投影 | E01/安装俯视投影 | E01/安装右视投影 | 数量与接口已定；产品适用认证/到货模板/实物验收待核 | A01 | 原厂工具压接；去漆接触面、防松并测连续性
E23 | 中央PE固定端M5环端子 | 电气采购 | E03 | 45 | E01/安装正视投影 | E01/安装俯视投影 | E01/安装右视投影 | 数量与接口已定；产品适用认证/到货模板/实物验收待核 | A01 | 各端独立夹紧；不得任意堆叠到短螺柱
E24 | 中央组件PE专用紧固件 | 电气采购 | E03 | 45 | E01/安装正视投影 | E01/安装俯视投影 | E01/安装右视投影 | 数量与接口已定；产品适用认证/到货模板/实物验收待核 | A01 | 各1套，螺纹朝上；不得兼用防坠或结构螺钉
H01 | 薄型调节脚 | 采购五金 | H02 | 50 | H02 安装接口 | 外购件，按厂家规格 | 外购件，按厂家规格 | 中国官方页有订购入口；库存未核 | A07 | TG-20；S03C内沉1，脚底名义外露5；每腿2只；调节后复核整桌900高及螺纹搭接；S03C脚孔局部u80/110、v13.9665，孔距30；不用原定制外φ18脚。厂家单件承载数据不能直接当整桌承载验收值。
H02 | M8六角焊接螺母 | 采购五金 | H02 | 50 | H02 安装接口 | 外购件，按厂家规格 | 外购件，按厂家规格 | 准确规格商品/可选规格页可网购；中国配送及实时库存未核 | S03C | DIN 929 M8 钢本色；S03C定位孔φ10.5 H11；不能沿用原φ8.5；焊后通规检查；不采用不锈钢/A2版本与碳钢底板直接混配。到货核对定位凸台和安装孔。
H03 | 检修门可脱卸合页 | 采购五金 | H03 | 51 | H03 安装接口 | 外购件，按厂家规格 | 外购件，按厂家规格 | 中国官方页有订购入口；库存未核 | S07 | HG-OTA75 / 170-090-942；每门2只；孔中心相对铰链展开中心为(±19, ±31.75)；轴线方向沿75边；M3穿透连接；两只标称6kg仅为厂家条件值。轴可缩入拆门；闭合不靠铰链阻尼，另设限位。
H04 | 直槽工具转舌锁（完整套件） | 采购五金 | H03 | 51 | H03 安装接口 | 外购件，按厂家规格 | 外购件，按厂家规格 | 国内厂家官方商城入口；须按完整套件型号订购并核库存 | S07 | MS705-1-1；适门T1~5，含35长舌、螺母、止退件；锁头法兰贴门底Z782，末端接触面H19.5为Z801.5；S10E接收顶Z801.3留0.2，不能按近轴GH18定位接收面。锁舌扫掠留净。；官网旧规格表写MS705-1-1.1，当前尺寸图写MS705-1-1；订货应随附本图，以35锁舌/直槽芯版本核对，不混54长舌版本。
H05 | 排插滑拆固定器组 | 采购五金 | H01 | 49 | H01 安装接口 | 外购件，按厂家规格 | 外购件，按厂家规格 | 厂家直链天猫成品；活动门应用为待验证候选 | S07 | LP332 / 每组2套；GN-604背部与喷涂门内面平整清洁，按厂家胶粘并充分固化；每组2套同向滑轨；不钻排插壳。活动门倒置、抗滑脱和热老化未获厂家证明，须连同用户插头做启闭/抗拉首件验证。；不把包装尺寸充当外形；承载额定、装配外包、店铺实时库存未核。
H06 | 承托盒白色穿线护口 | 采购五金 | H01 | 49 | H01 安装接口 | 外购件，按厂家规格 | 外购件，按厂家规格 | 可网购具体型号；到货φ50孔配装及入孔深待复核 | W03A | 429.99.735；W03A长侧T15板φ50孔；局部u165/v51，全局(600/1400,492.5,842)，孔朝近侧-Y。筒向盒内突出约7；保持周围净空，按厂家允许压装或胶粘。可取盖穿原装插头，再恢复护口；开口及插头穿越须首件核实。；S51/WHT孔径44.2与本项目不符，已排除；不改原φ50孔为错规格。
H07 | 小翻盖隐藏桶式铰链 | 采购五金 | H03 | 51 | H03 安装接口 | 外购件，按厂家规格 | 外购件，按厂家规格 | 厂家官网可加入购物车；中国现货和进口交期未核 | A03 | BH104；T18盖及桌面均从顶面钻φ10深11.5；剩板厚6.5。每盖u50/248、孔心距外侧开合边6.8；180°展开对应桌面闭合共面，操作抬90°。；厂家仅轻型应用，无扭矩保持；闭合须8只独立角码支承。顶面可见桶式铰链金属链节；低Y毛刷安装28×7槽保留，不能误删。
H09 | 桌面M6机螺钉 | 采购五金 | H02 | 50 | H02 安装接口 | 外购件，按厂家规格 | 外购件，按厂家规格 | 准确规格商品/可选规格页可网购；中国配送及实时库存未核 | A03 | ISO 4762 / DIN 912 M6×12；穿T3固定耳＋T1.6垫片，进入桌面嵌母7.4；由桌下拆装；成对点X580/850/1150/1420×Y328/872；8点为R02设计数量；拧紧扭矩按实际阻燃多层板试验，不能套用钢连接满扭矩。
H10 | 桌面M6木用嵌入螺母 | 采购五金 | H02 | 50 | H02 安装接口 | 外购件，按厂家规格 | 外购件，按厂家规格 | 厂家官网可在线订购；中国现货和进口交期未核 | W01 | SKD30 439612001；从桌面底安装；试样底孔φ10.5深14、面层最小保留4；嵌件法兰与底面齐，深度限位钻孔；底孔深14是本项目T18安全余量设计，厂家仅提供底孔直径范围；在同批阻燃板试装/拔出检查后放行。不拿京东泛称M6×12未知外径件直接代换。
H11 | M6平垫圈 | 采购五金 | H02 | 50 | H02 安装接口 | 外购件，按厂家规格 | 外购件，按厂家规格 | 准确规格商品/可选规格页可网购；中国配送及实时库存未核 | A03 | ISO 7089 / DIN 125-A 6；与8只M6×12配套；覆盖6.6×12长圆调节孔；不要用不同厚度弹垫替代，否则有效啮合长度变化。
H12 | 检修门合页螺钉配套 | 采购五金 | H03 | 51 | H03 安装接口 | 外购件，按厂家规格 | 外购件，按厂家规格 | 准确规格商品/可选规格页可网购；中国配送及实时库存未核 | S07 | M3×8盘头＋M3防松螺母＋M3平垫；穿φ3.8合页孔与门/底盘配孔；每套1螺钉1平垫1防松螺母；组装后验轴芯可操作；合页叶片T1.5＋门T1.5（或支撑板）；M3×8避免长端侵入活动区。
H13 | 检修盖及吊板防脱螺钉 | 采购五金 | H02 | 50 | H02 安装接口 | 外购件，按厂家规格 | 外购件，按厂家规格 | NBK中国官方询价/官方1688渠道；库存未核 | A04 | SSC-M5-8；中央盖4：T1.5攻M5防脱＋T1底盘＋T2补强＋DIN929 M5，夹紧栈4.5，啮合3.5。吊板4：T2攻M5防脱＋T3臂＋DIN929 M5，夹紧栈5，啮合3。；盖4点(840/1160,450/750)；吊板4点(890/1110,470/730)。SSC末牙4、颈4；不换长10型号。
H25 | 成品过线衬套 | 采购五金 | A06 | 52 | A06 安装接口 | 外购件，按厂家规格 | 外购件，按厂家规格 | 厂家美国官网可按只加购物车；中国配送和库存未核 | A06 | CHC-S18BL；W01孔φ14+0.5/0；按桌面/设备过线设计装20只；衬套面高出桌面2；替代R01 M01/M02定制金属护套。数量与桌面接口由主装配核对，不凭图示符号加计。
H26 | 闲置孔成品盖 | 采购五金 | A06 | 52 | A06 安装接口 | 外购件，按厂家规格 | 外购件，按厂家规格 | 国外经销商网购500只/包；单桌用10只，中国配送及实时库存未核 | A06 | 045.00.332；装入CHC-S18BL内φ12；组合总突出约4；首件实配通过前不得当认证配套；与LAMP衬套属于跨品牌组合，需确认卡紧、拔出力及顶高；不伪称厂家认证套装。
H14 | 检修盖及吊板M5焊接螺母 | 采购五金 | H02 | 50 | H02 安装接口 | 外购件，按厂家规格 | 外购件，按厂家规格 | 准确规格商品/可选规格页可网购；中国配送及实时库存未核 | A04 | DIN929 M5 钢本色；盖T2补强片或吊板T3臂均φ7 H11定位后焊；盖4、板4；对应SSC-M5-8。；订单具体SKU、包装量和库存待采购核对。
H15 | 横梁M6连接螺钉配套 | 采购五金 | H02 | 50 | H02 安装接口 | 外购件，按厂家规格 | 外购件，按厂家规格 | 准确规格商品/可选规格页可网购；中国配送及实时库存未核 | S09A | ISO4762 M6×20＋ISO7089平垫6；C筋T2＋每螺栓4mm调整片＋S09A T3端板＋DIN929M6；每端2点，共16套。；订单具体SKU、包装量和库存待采购核对。
H16 | 横梁M6焊接螺母 | 采购五金 | H02 | 50 | H02 安装接口 | 外购件，按厂家规格 | 外购件，按厂家规格 | 准确规格商品/可选规格页可网购；中国配送及实时库存未核 | S09A | DIN929 M6 钢本色；S09A T3端板φ8 H11；焊母朝管腔；孔心(30,18)/(30,42)；订单具体SKU、包装量和库存待采购核对。
H17 | 承托盒M4连接螺钉配套 | 采购五金 | H02 | 50 | H02 安装接口 | 外购件，按厂家规格 | 外购件，按厂家规格 | 准确规格商品/可选规格页可网购；中国配送及实时库存未核 | S09C | M4×25＋M4平垫；轴水平X；穿木板φ4.5后入抱角焊母；订单具体SKU、包装量和库存待采购核对。
H18 | 承托盒M4焊接螺母 | 采购五金 | H02 | 50 | H02 安装接口 | 外购件，按厂家规格 | 外购件，按厂家规格 | 准确规格商品/可选规格页可网购；中国配送及实时库存未核 | S09C | DIN929 M4 钢本色；T2抱角φ6 H11定位焊；与M4×25配套；订单具体SKU、包装量和库存待采购核对。
H19 | 翻盖独立承托角码 | 采购五金 | H03 | 51 | H03 安装接口 | 外购件，按厂家规格 | 外购件，按厂家规格 | 成品或标准件可订购；未下单、实时库存未核 | A03 | SU-30S / 120-030-070；每盖两短端各1只；角码钢顶Z882−实测含胶软垫厚（名义879.77）；X450..480/720..750及+800；Y中心552/648；厂家安装目录配长螺钉会穿T15板，本项目另购φ3×12；水平面不锁翻盖。
H20 | 角码木螺钉 | 采购五金 | H03 | 51 | H03 安装接口 | 外购件，按厂家规格 | 外购件，按厂家规格 | 准确规格商品/可选规格页可网购；中国配送及实时库存未核 | A03 | WV007880 / φ3×12沉头TX10；经T2.5角码横向入T15板约9.5；预钻孔径按实际木料试样，深度限位；订单具体SKU、包装量和库存待采购核对。
H21 | 角码软垫 | 采购五金 | H03 | 51 | H03 安装接口 | 外购件，按厂家规格 | 外购件，按厂家规格 | 德国厂家网店可下单1片；国内配送和库存未核 | A03 | 100191 / EAN4260627935185；含胶名义2.23；按实测总厚定位角码钢顶Z882−实测厚，使软垫顶882；Shore A约65；每桌切8片净面积2304mm²；1片原板足够。含胶厚必须到货实测。
B01 | 成品毛刷条 | 采购五金 | H01 | 49 | H01 安装接口 | 外购件，按厂家规格 | 外购件，按厂家规格 | 成品或标准件可订购；未下单、实时库存未核 | A03 | RS PRO 326-9808；切160+298+500+298+160=1416；4处1缝合计覆盖1420；低Y侧28×7槽，刷毛向+Y，尖端留1；两个298段随W02A翻盖，其余3段固定W01；采购2m含584mm下料余量；取消不明B02挡条。
B03 | 毛刷固定木螺钉 | 采购五金 | H01 | 49 | H01 安装接口 | 外购件，按厂家规格 | 外购件，按厂家规格 | 准确规格商品/可选规格页可网购；中国配送及实时库存未核 | A03 | 000338aa230623qmaneu / φ3×8；成品铝型材自配φ3.5孔；不得把型材截面剪短；木板槽后余厚11，限深避免穿面；订单具体SKU、包装量和库存待采购核对。
H22 | 横梁调整垫片 | 采购五金 | H02 | 50 | H02 安装接口 | 外购件，按厂家规格 | 外购件，按厂家规格 | 厂家网店100片/包可加入购物车；国内配送和库存未核 | S09A | W29338 / DIN988 6×12×1；16个M6螺栓位置×4片=64；每端2螺栓8片；使478总长梁装入486内净距；成品调整片，不能按8个梁端误计32；安装实测总厚及孔径通过性。
H23 | 检修盖及吊板防坠索 | 采购五金 | H01 | 49 | H01 安装接口 | 外购件，按厂家规格 | 外购件，按厂家规格 | 经销网店可加入购物篮但页面无现货；须核交期及中国配送 | A04 | GN111.2-150-C-BL；盖2根、吊板2根；载板平差X40/Y20、初始Z差2，下放约175.45；盖竖挂平差10、上下差182.73；有效长度按实物核；厂家1800N是静载参考，非动态跌落额定。固定端片两面大垫夹持，盖/吊板下放全过程托住，防坠仅兜底。
H24 | 防坠索端片紧固配套 | 采购五金 | H01 | 49 | H01 安装接口 | 外购件，按厂家规格 | 外购件，按厂家规格 | 螺钉准确型号可网购；套内垫圈与螺母分购，国内配送及库存未核 | A04 | ISO7045 M4×16＋2×DIN9021 M4＋DIN985 M4；悬臂螺钉从上向下，头＋上垫最大4.25；端片直接贴钢件下侧，下垫及防松母夹紧；木底净0.75；悬臂T3＋两垫T1＋端片T1.5＋防松母高5，M4×16末端余4.5；已核下方不撞梁/箱体。盖锚(860/1140,440)，底盘锚同X、Y400。
A06 | 成品护口与孔盖组件 | 装配 | A06 | 52 | A06 轴向剖面 | A06 俯视 | A06 轴对称右视 | 首件跨品牌配装待核 | A03 | 成品H25/H26替代R01机加工M01/M02/M03；装配计数不叠加采购子件。

Sheet: 复核记录
交付资料复核记录
HW73005-L2000 L2000体验桌 R03 尺寸单位 mm
批量（套） | 1 | 版次日期 | 2026-10-01
记录资料内部校核及尚待确认的事项；不代表工厂或接收方已批准下单。
类别 | 复核对象 | 结果 | 证据 / 处理说明
图纸页数 | R03 | 52 | 第3轮构建
零件条目数 | R03 | 84 | 第3轮构建
三维装配实例数 | R03 | 449 | 第3轮构建
待建模零件 | R03 | 无 | 第3轮构建
原生尺寸标注数 | R03 | 212 | 第3轮构建
CAD审计错误数 | R03 | 0 | 第3轮构建
CAD审计修复数 | R03 | 0 | 第3轮构建
尺寸数值覆写 | R03 | 无 | 第3轮构建
零件编号一致 | R03 | 通过 | 第3轮构建
图号关联完整 | R03 | 通过 | 第3轮构建
图面目检 | R03 | 52页图面分工目检通过；末轮3张重点图独立复核通过；不含接收方CAD及工厂首件 | 第三轮：root总览及索引14页、机械33有效页、电气6页；重叠总装1页；atlas末轮3页独立复核
接收方CAD验收 | R03 | 未执行 | 第3轮构建
工厂首件验收 | R03 | 未执行 | 第3轮构建
原生三维实例数 | R03 | 449 | 第3轮构建
原生三维图纸索引绑定 | R03 | 通过 | 第3轮构建
